huyhoanghust/Final-Project/DATASHEET/RS232_9_pin_D.png

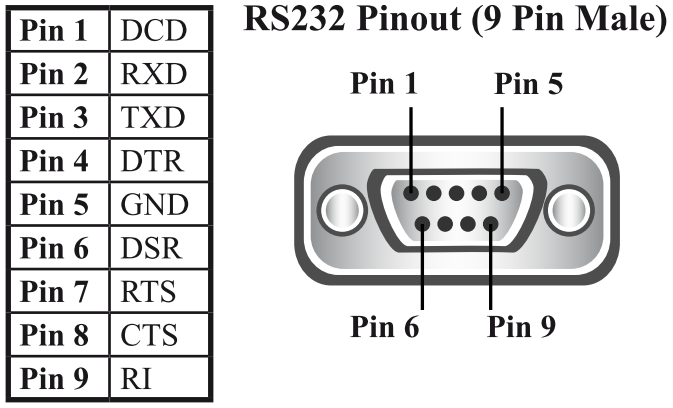
DATASHEET/RS232_9_pin_D.png
