huyhoanghust/Final-Project/DATASHEET/tps54260.png

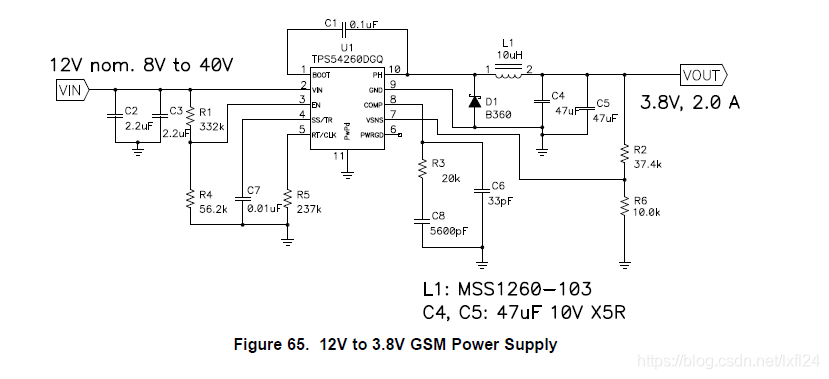
DATASHEET/tps54260.png
