huyhoanghust/Final-Project/DOCUMENT/PICTURE/bang-ky-su-cap-thoat-nuoc-2.jpeg

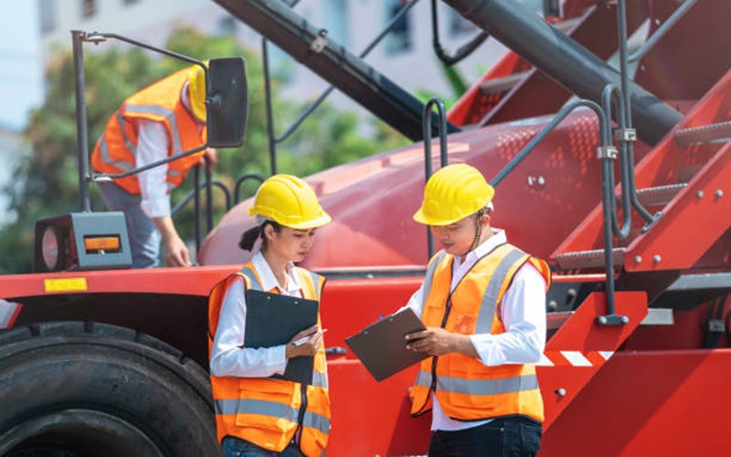
DOCUMENT/PICTURE/bang-ky-su-cap-thoat-nuoc-2.jpeg
