huyhoanghust/Final-Project/DOCUMENT/PICTURE/{1DA086E6-415D-411F-91D1-63A72A324FEF}.png.jpg

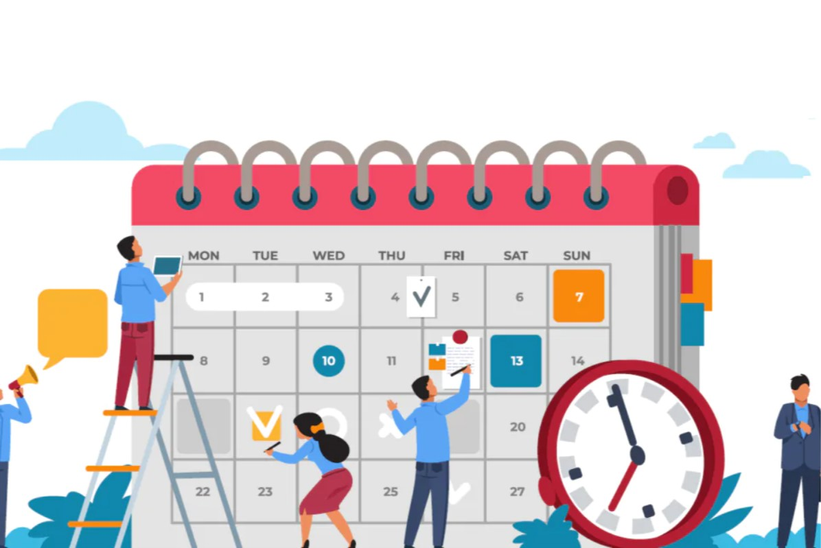
DOCUMENT/PICTURE/{1DA086E6-415D-411F-91D1-63A72A324FEF}.png.jpg
