huyhoanghust/Final-Project/DOCUMENT/PICTURE/{3720CE3A-4CB5-49F4-AB9C-371806BE8C6B}.png.jpg

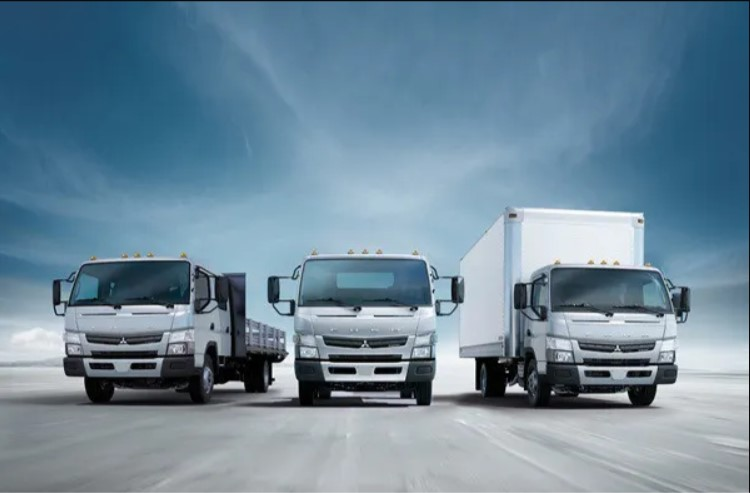
DOCUMENT/PICTURE/{3720CE3A-4CB5-49F4-AB9C-371806BE8C6B}.png.jpg
