huyhoanghust/Final-Project/DOCUMENT/PICTURE/{B581A70F-E1D5-4213-A3DD-116B70B1F578}.png.jpg

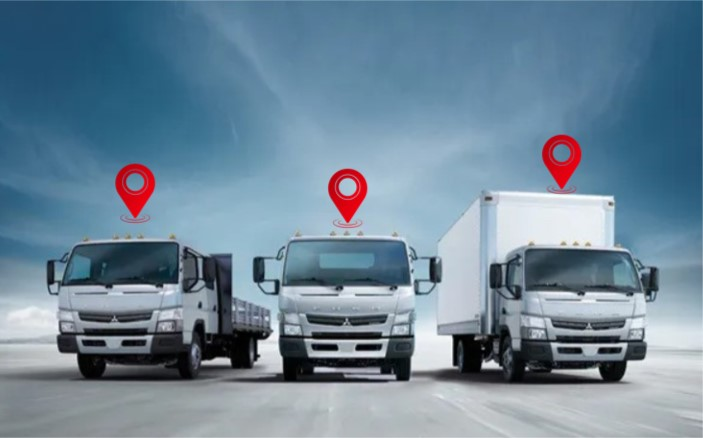
DOCUMENT/PICTURE/{B581A70F-E1D5-4213-A3DD-116B70B1F578}.png.jpg
