huyhoanghust/Final-Project/DOCUMENT/PICTURE/{C75D569E-5FCE-4055-875E-4021B6C22FDB}.png.jpg

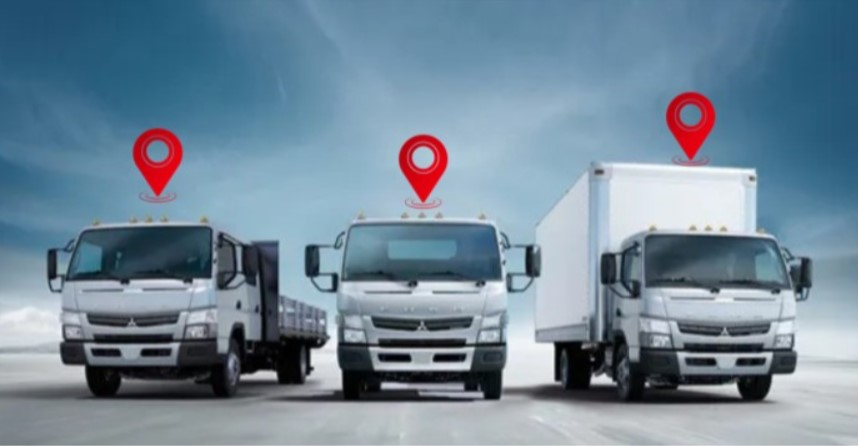
DOCUMENT/PICTURE/{C75D569E-5FCE-4055-875E-4021B6C22FDB}.png.jpg
