huyhoanghust/Final-Project/kế hoạch BVTN.jpg

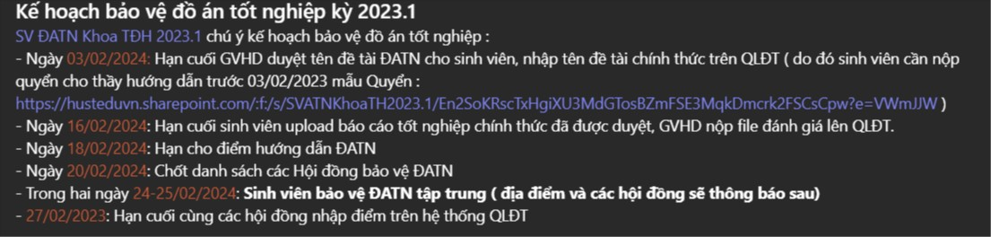
kế hoạch BVTN.jpg
