huyhoanghust/Final-Project/PICTURE/44d2d4de8f7726297f664.jpg

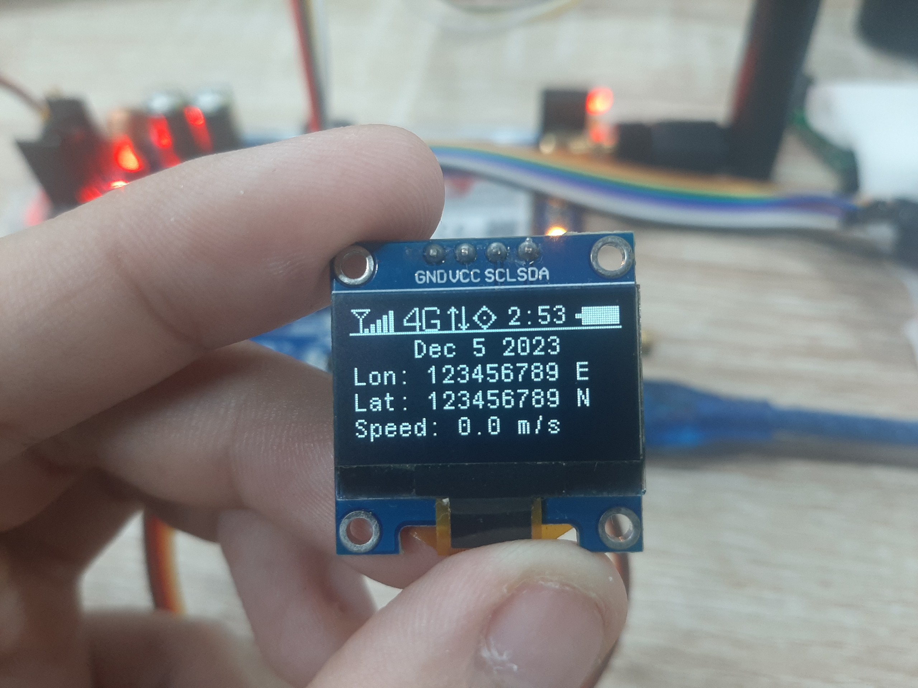
PICTURE/44d2d4de8f7726297f664.jpg
