huyhoanghust/Final-Project/PICTURE/93d33e26648fcdd1949e1.jpg

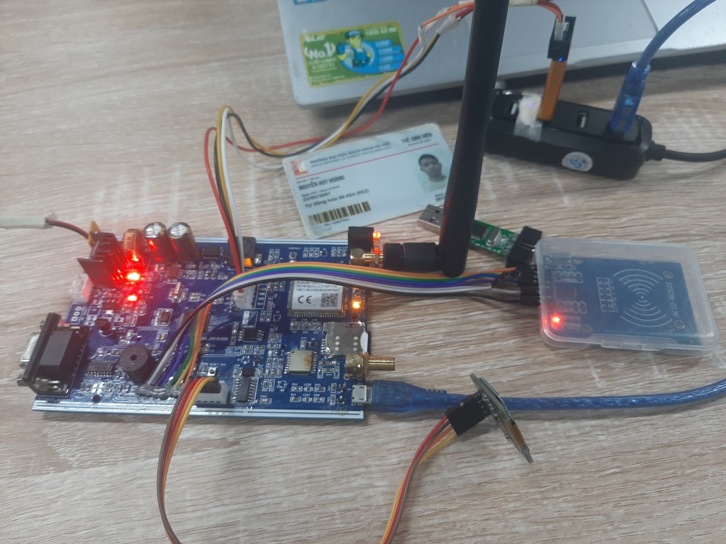
PICTURE/93d33e26648fcdd1949e1.jpg
