huyhoanghust/Final-Project/PICTURE/c10f670b3ca295fcccb33.jpg

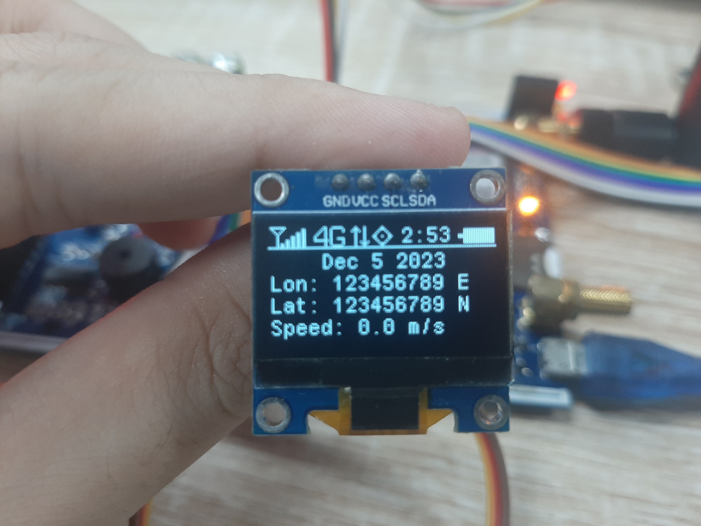
PICTURE/c10f670b3ca295fcccb33.jpg
