huyhoanghust/Final-Project/PICTURE/dfdee423be8a17d44e9b2.jpg

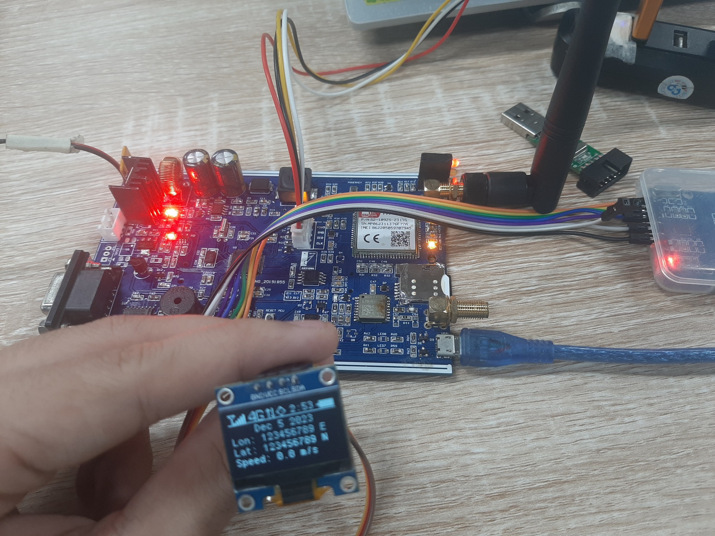
PICTURE/dfdee423be8a17d44e9b2.jpg
