huyhoanghust/Final-Project/PICTURE/f30cfbd6628cc9d2909d.jpg

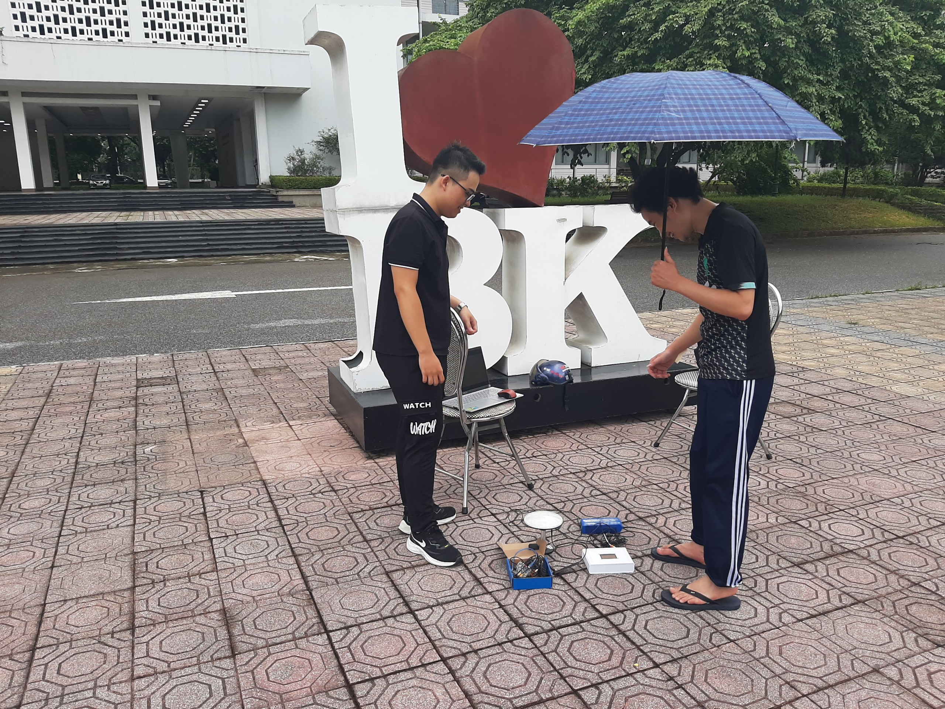
PICTURE/f30cfbd6628cc9d2909d.jpg
