huyhoanghust/Final-Project/PICTURE/firm/ĐATN-firm1.drawio.png

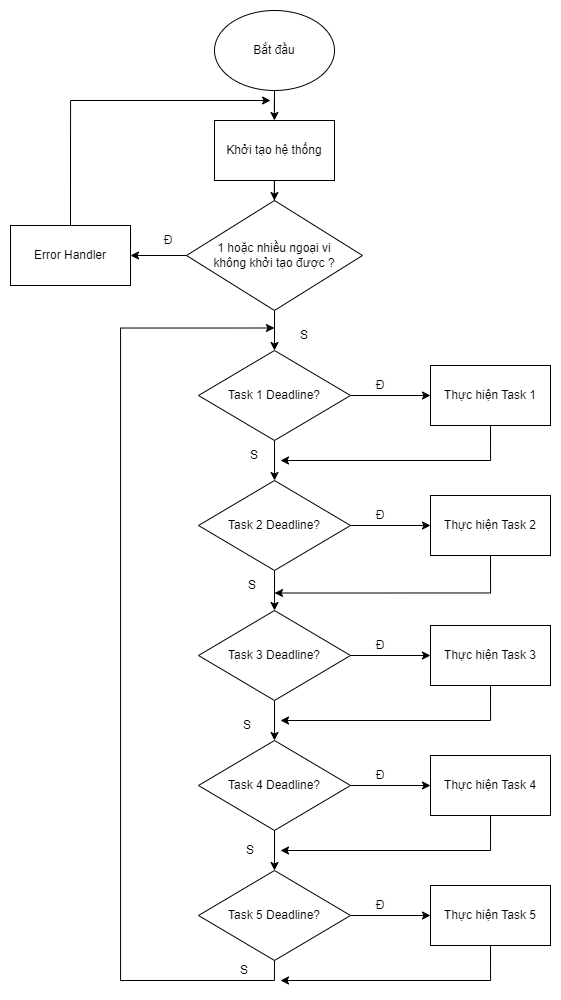
PICTURE/firm/ĐATN-firm1.drawio.png
