huyhoanghust/Final-Project/PICTURE/firm/ĐATN-firm2.drawio.png

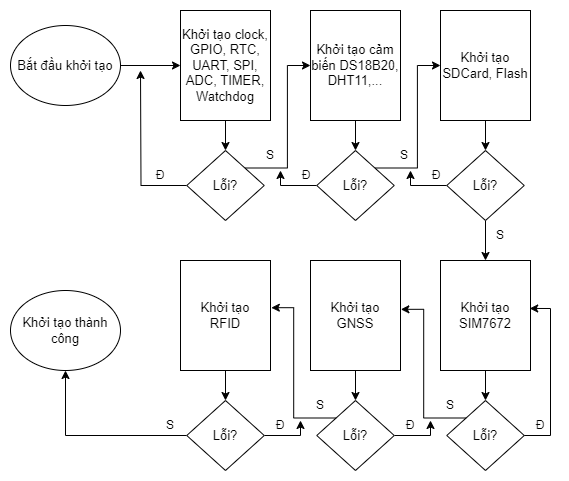
PICTURE/firm/ĐATN-firm2.drawio.png
