huyhoanghust/Final-Project/PICTURE/gnss/bản tin MTK NMEA.jpg

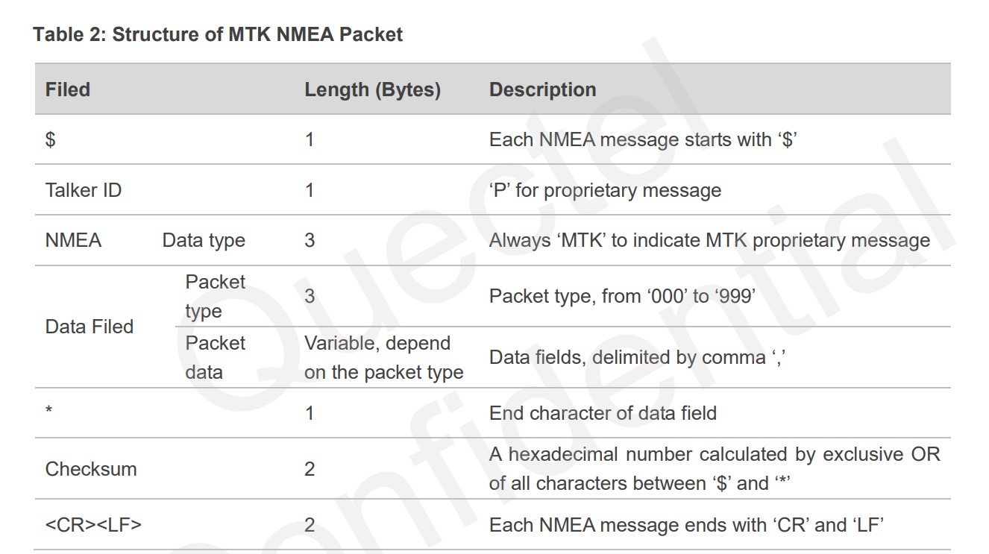
PICTURE/gnss/bản tin MTK NMEA.jpg
