huyhoanghust/Final-Project/PICTURE/gnss/bản tin NMEA.jpg

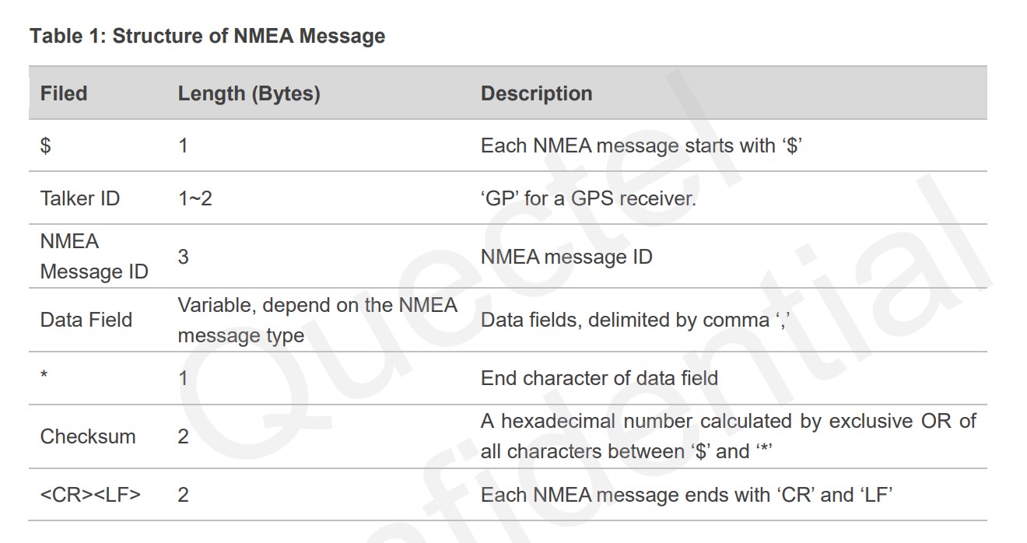
PICTURE/gnss/bản tin NMEA.jpg
