huyhoanghust/Final-Project/PICTURE/gnss/decodeer.jpg

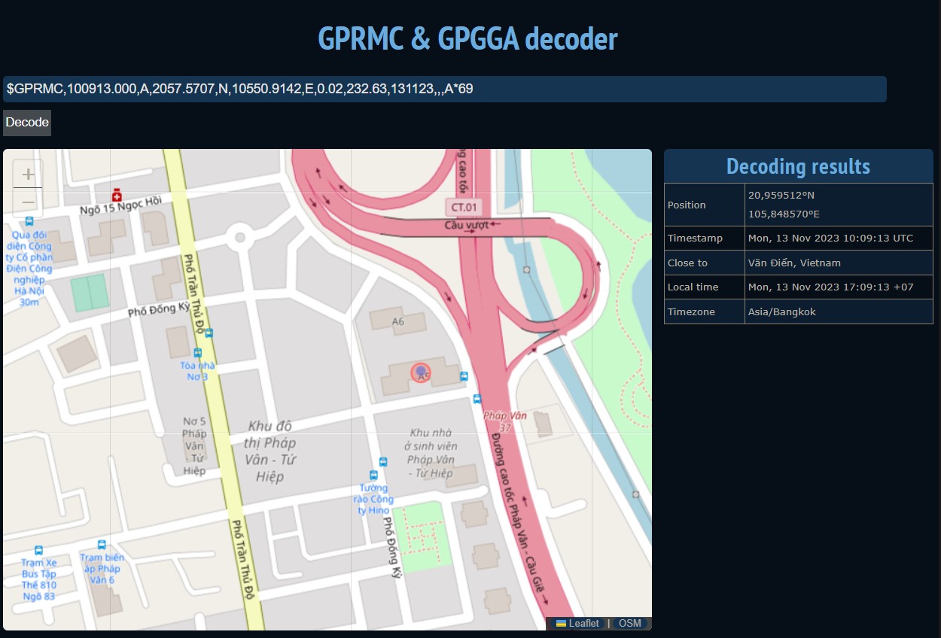
PICTURE/gnss/decodeer.jpg
