huyhoanghust/Final-Project/PICTURE/gnss/{8CABD70A-028F-4958-99A2-55783BED586A}.png.jpg

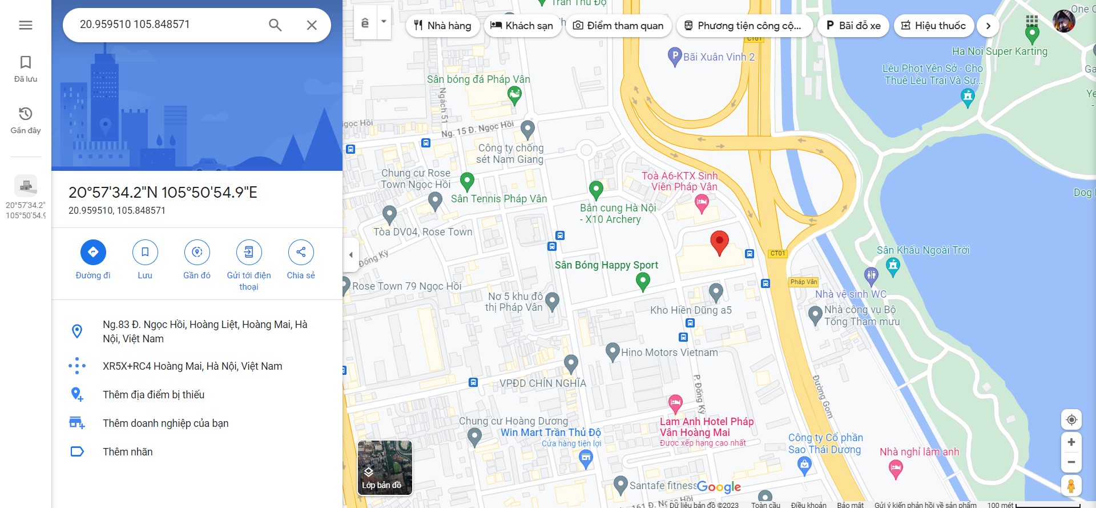
PICTURE/gnss/{8CABD70A-028F-4958-99A2-55783BED586A}.png.jpg
