huyhoanghust/Final-Project/PICTURE/gnss/{868871F9-2B1D-4495-A387-216AAB7A92D2}.png.jpg

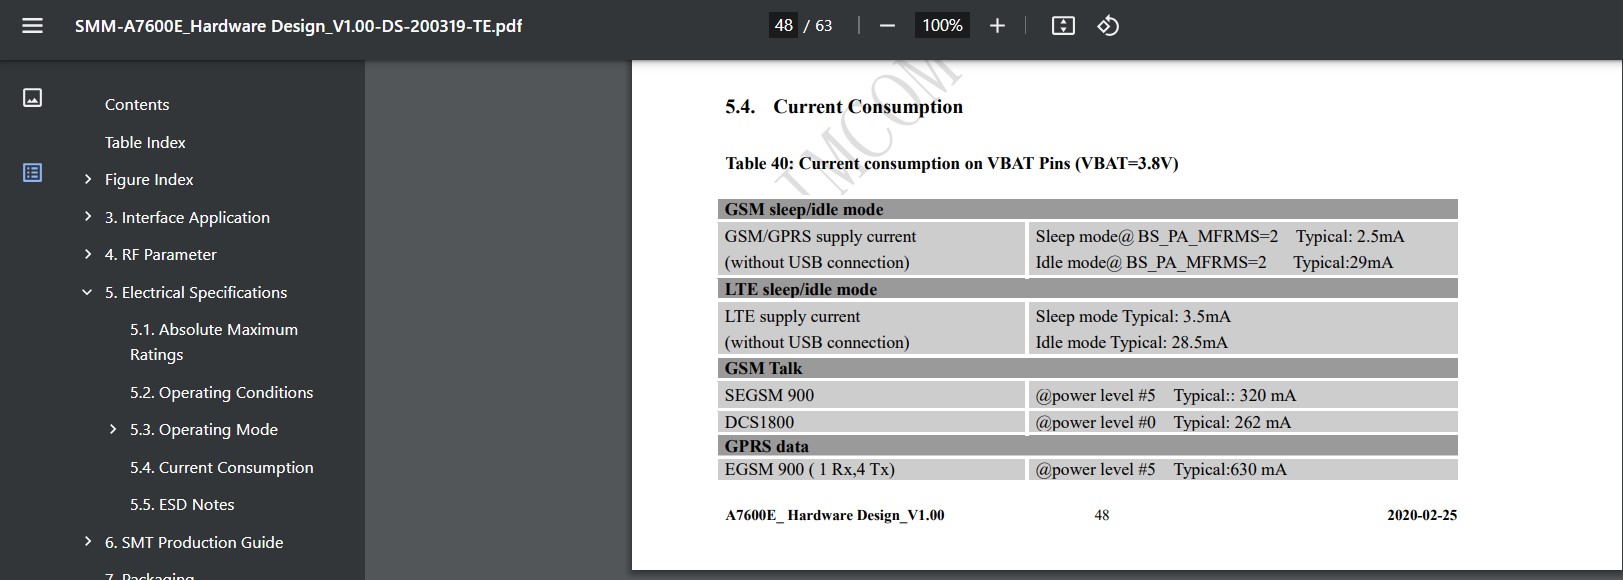
PICTURE/gnss/{868871F9-2B1D-4495-A387-216AAB7A92D2}.png.jpg
