huyhoanghust/Final-Project/PICTURE/gnss/ĐATN-l70_command.drawio.png

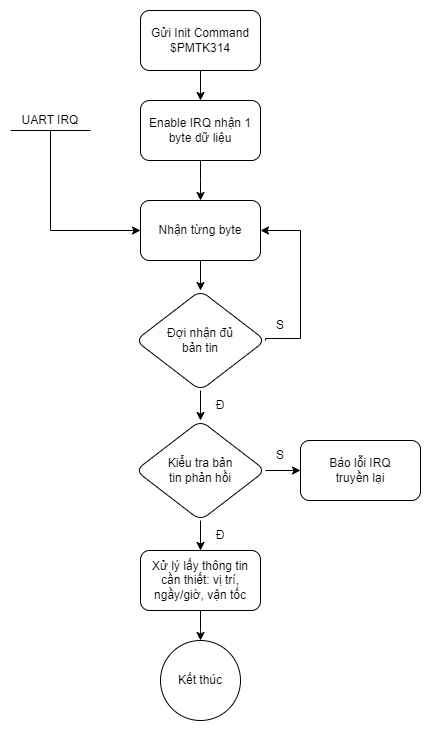
PICTURE/gnss/ĐATN-l70_command.drawio.png
