huyhoanghust/Final-Project/PICTURE/hộp/6137ed7632019a5fc31013.jpg

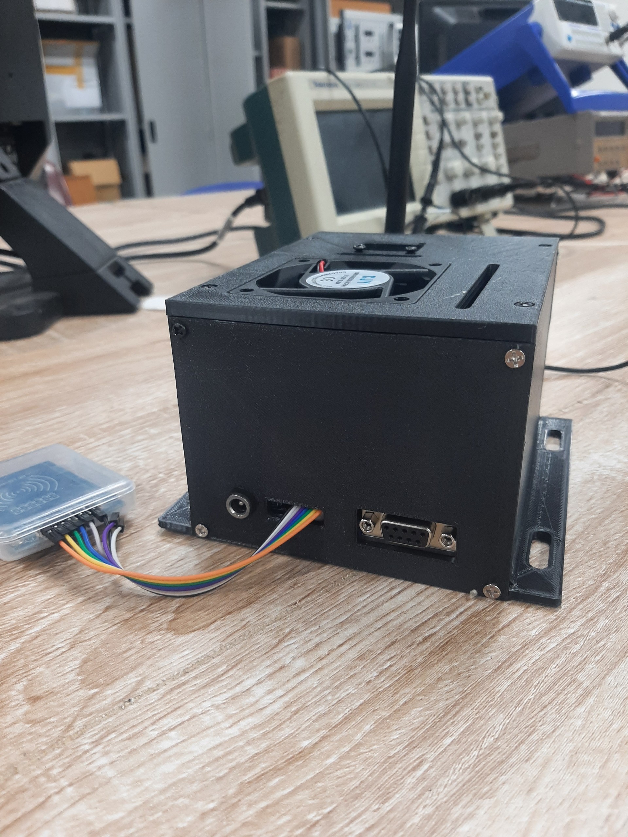
PICTURE/hộp/6137ed7632019a5fc31013.jpg
