huyhoanghust/Final-Project/PICTURE/hộp/64983ceee3994bc7128814.jpg

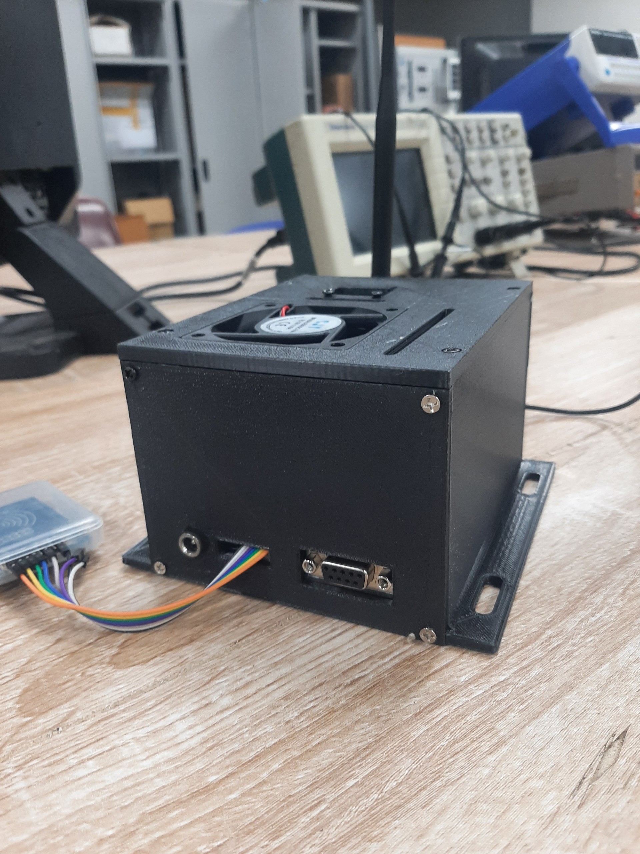
PICTURE/hộp/64983ceee3994bc7128814.jpg
