huyhoanghust/Final-Project/PICTURE/hộp/b8e8435f9c2834766d3911.jpg

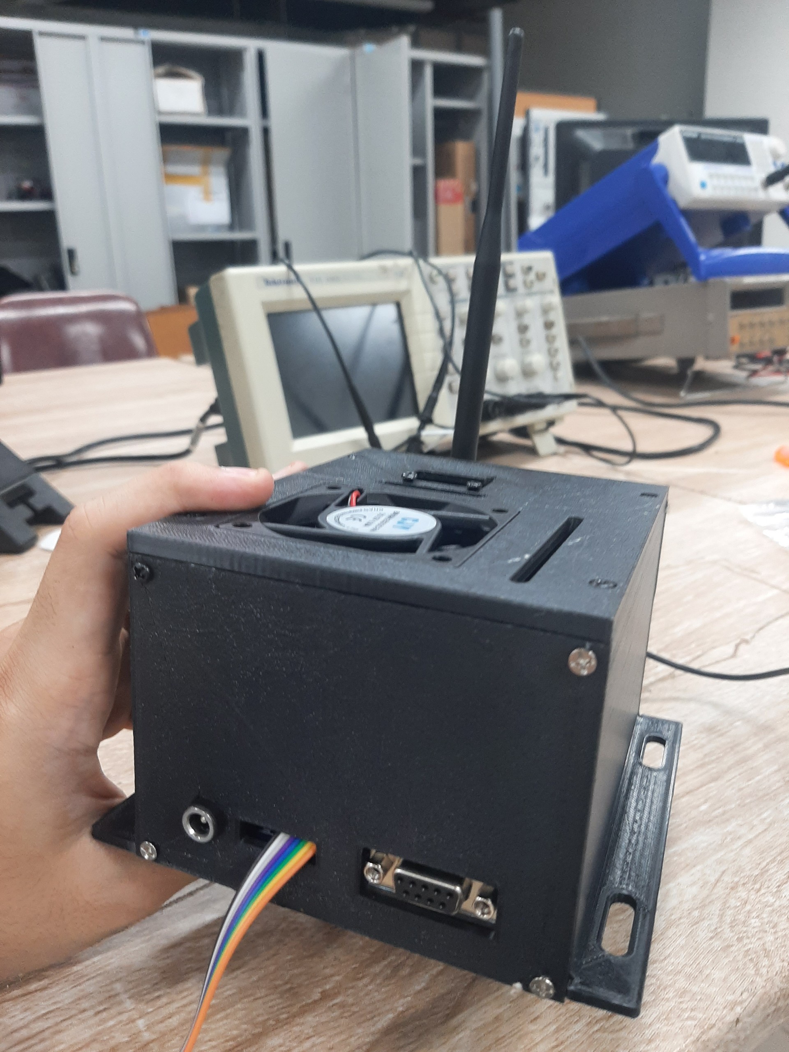
PICTURE/hộp/b8e8435f9c2834766d3911.jpg
