huyhoanghust/Final-Project/PICTURE/hộp/d4fb86a159d6f188a8c712.jpg

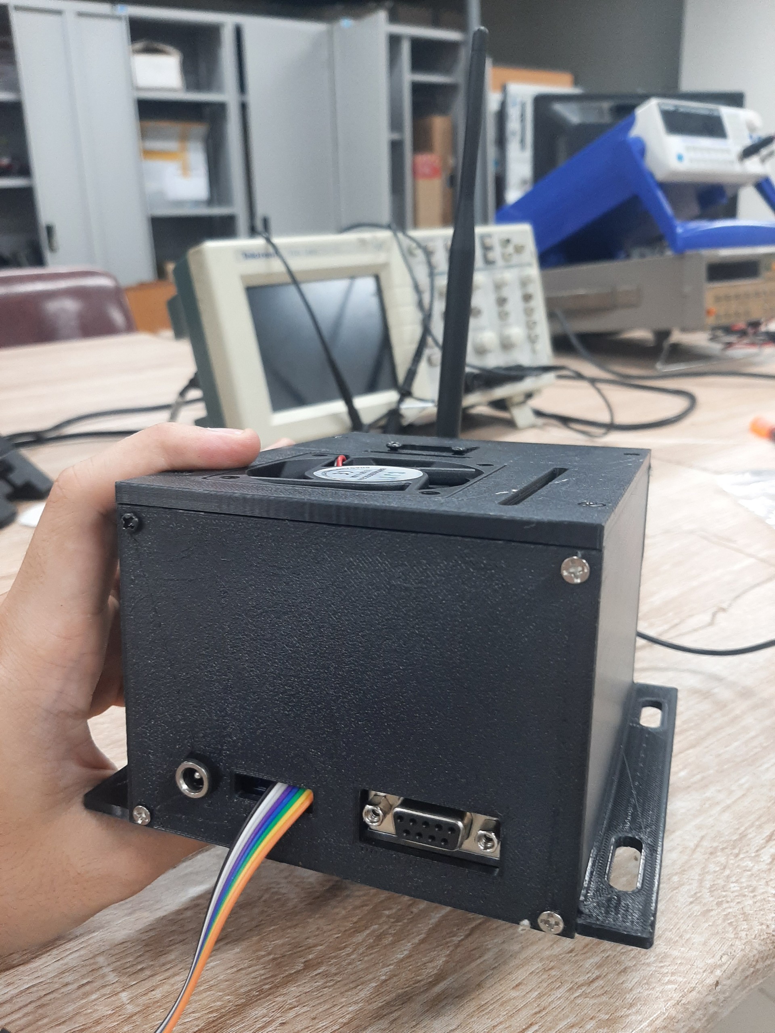
PICTURE/hộp/d4fb86a159d6f188a8c712.jpg
