huyhoanghust/Final-Project/PICTURE/hộp/Vỏ hộp/99a54a46c971602f39606.jpg

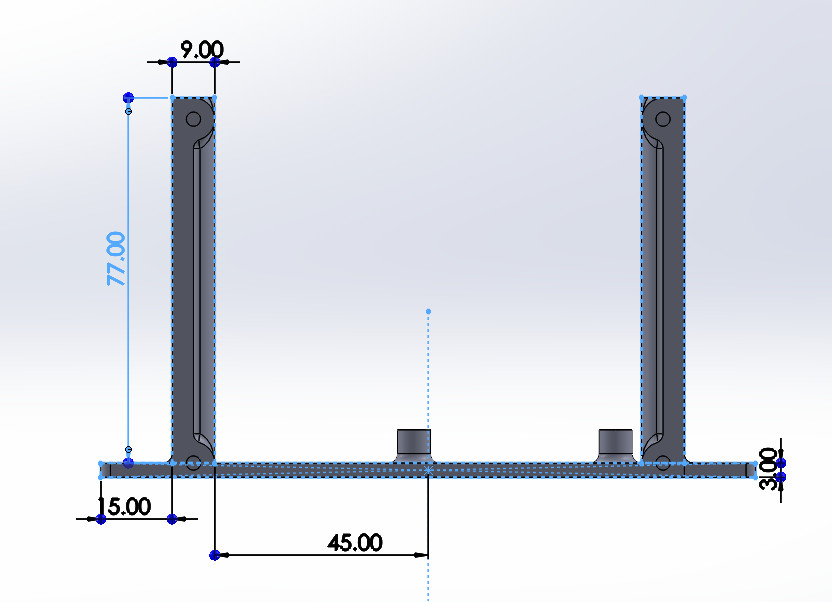
PICTURE/hộp/Vỏ hộp/99a54a46c971602f39606.jpg
