huyhoanghust/Final-Project/PICTURE/hộp/Vỏ hộp/100a95e716d0bf8ee6c15.jpg

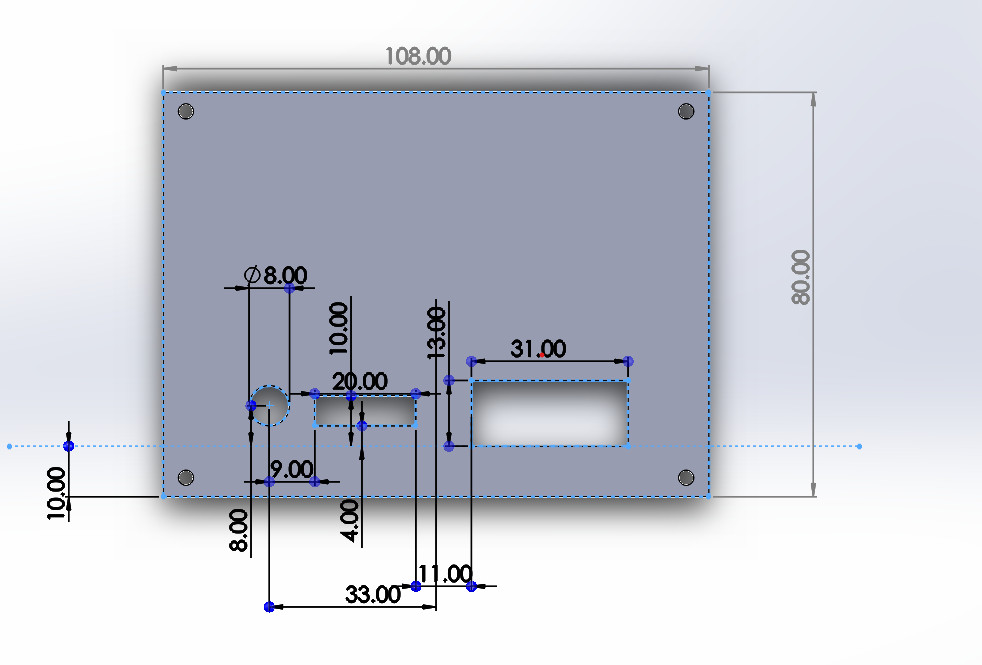
PICTURE/hộp/Vỏ hộp/100a95e716d0bf8ee6c15.jpg
