huyhoanghust/Final-Project/PICTURE/jack.jpeg

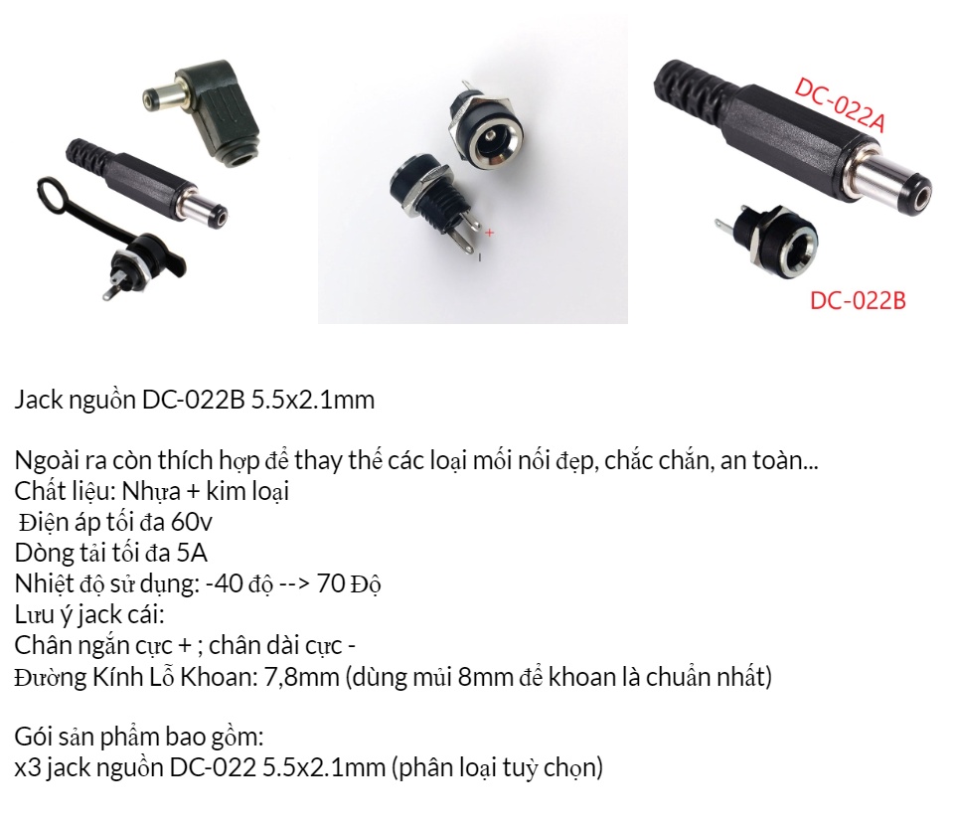
PICTURE/jack.jpeg
