huyhoanghust/Final-Project/PICTURE/kịch bản thử nghiệm/kịch bản 2.jpg

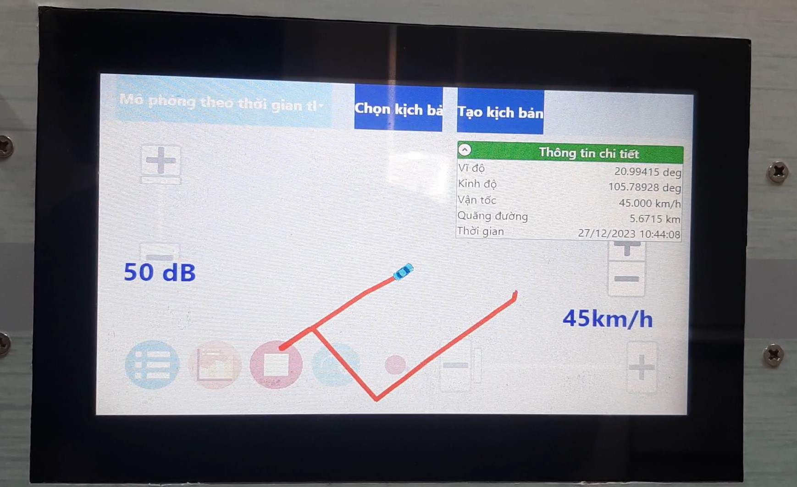
PICTURE/kịch bản thử nghiệm/kịch bản 2.jpg
