huyhoanghust/Final-Project/PICTURE/kịch bản thử nghiệm/máy phát gps.jpg

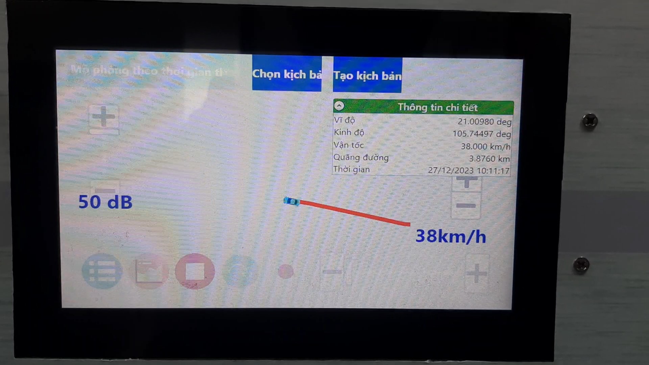
PICTURE/kịch bản thử nghiệm/máy phát gps.jpg
