huyhoanghust/Final-Project/PICTURE/kịch bản thử nghiệm/{20B134B7-DE23-4ED3-82E7-74394B83585F}.png.jpg

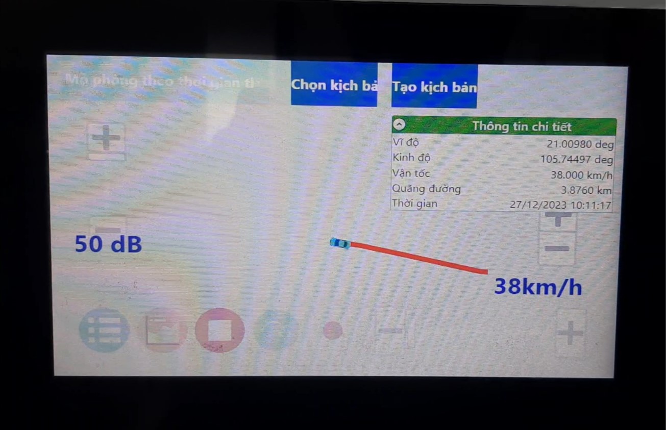
PICTURE/kịch bản thử nghiệm/{20B134B7-DE23-4ED3-82E7-74394B83585F}.png.jpg
