huyhoanghust/Final-Project/PICTURE/kịch bản thử nghiệm/{F6EBA6C6-F068-47A6-98E9-1B882EAFC6DC}.png.jpg

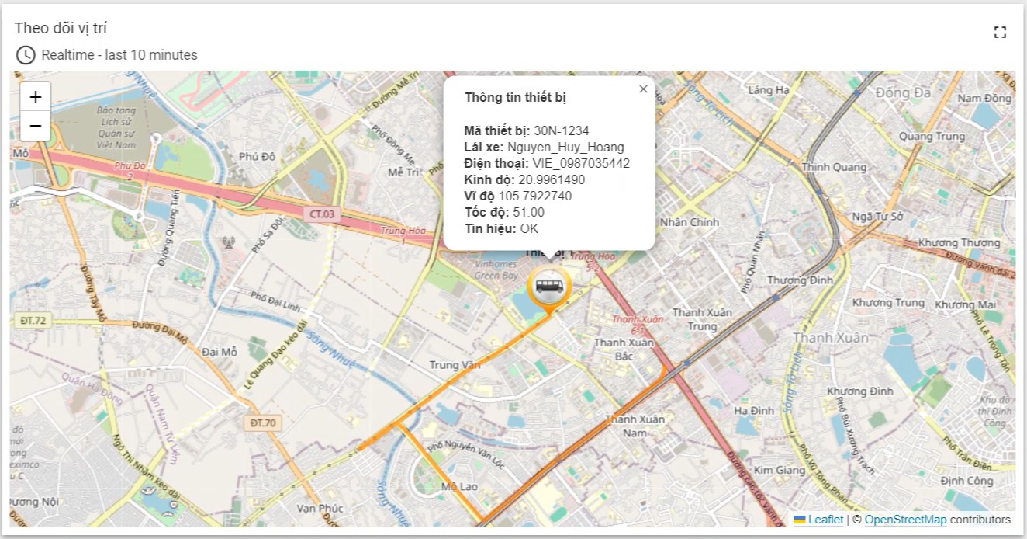
PICTURE/kịch bản thử nghiệm/{F6EBA6C6-F068-47A6-98E9-1B882EAFC6DC}.png.jpg
