huyhoanghust/Final-Project/PICTURE/kịch bản thử nghiệm/đại lộ Thăng Long.jpg

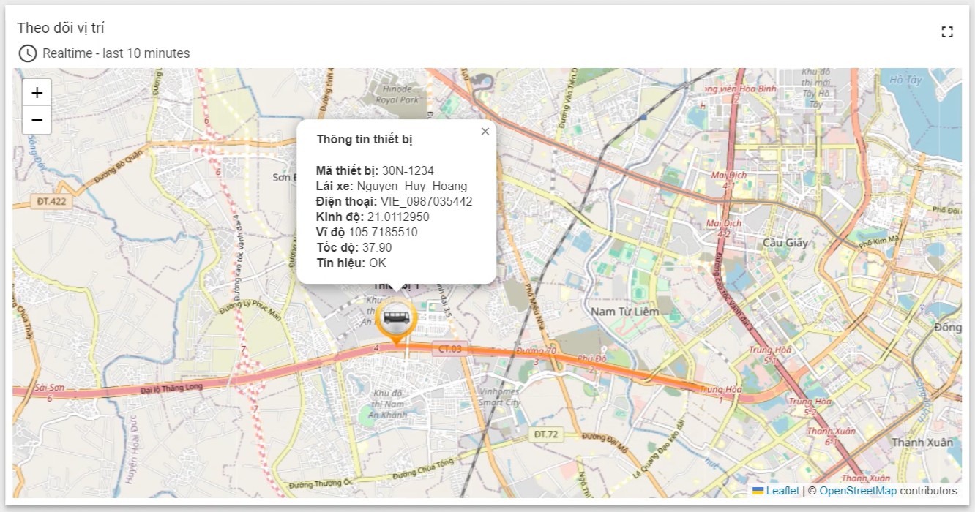
PICTURE/kịch bản thử nghiệm/đại lộ Thăng Long.jpg
