huyhoanghust/Final-Project/PICTURE/Netlight.jpg

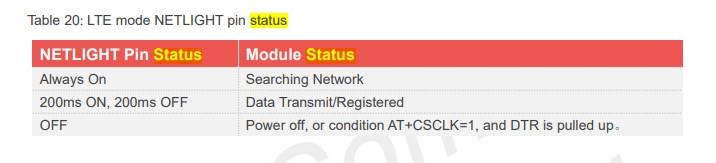
PICTURE/Netlight.jpg
