huyhoanghust/Final-Project/PICTURE/pcb/0be75f5d5223fa7da3328.jpg

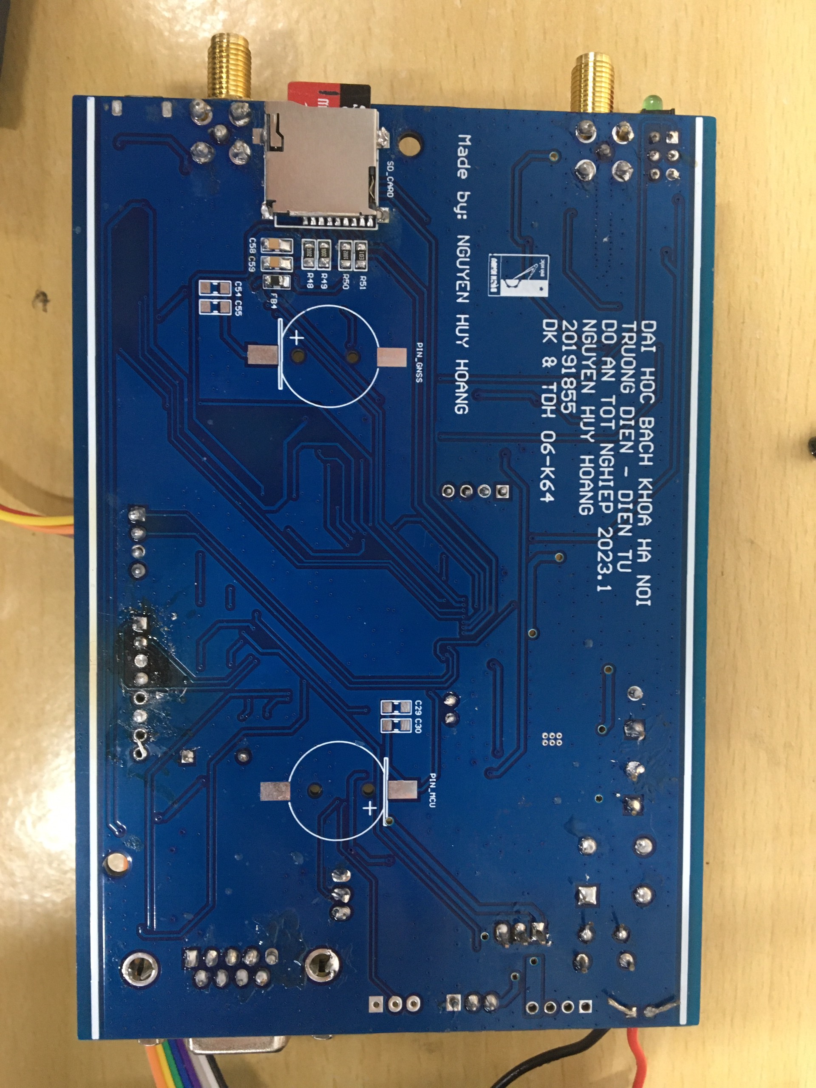
PICTURE/pcb/0be75f5d5223fa7da3328.jpg
