huyhoanghust/Final-Project/PICTURE/pcb/5a7ebb8eb6f01eae47e16.jpg

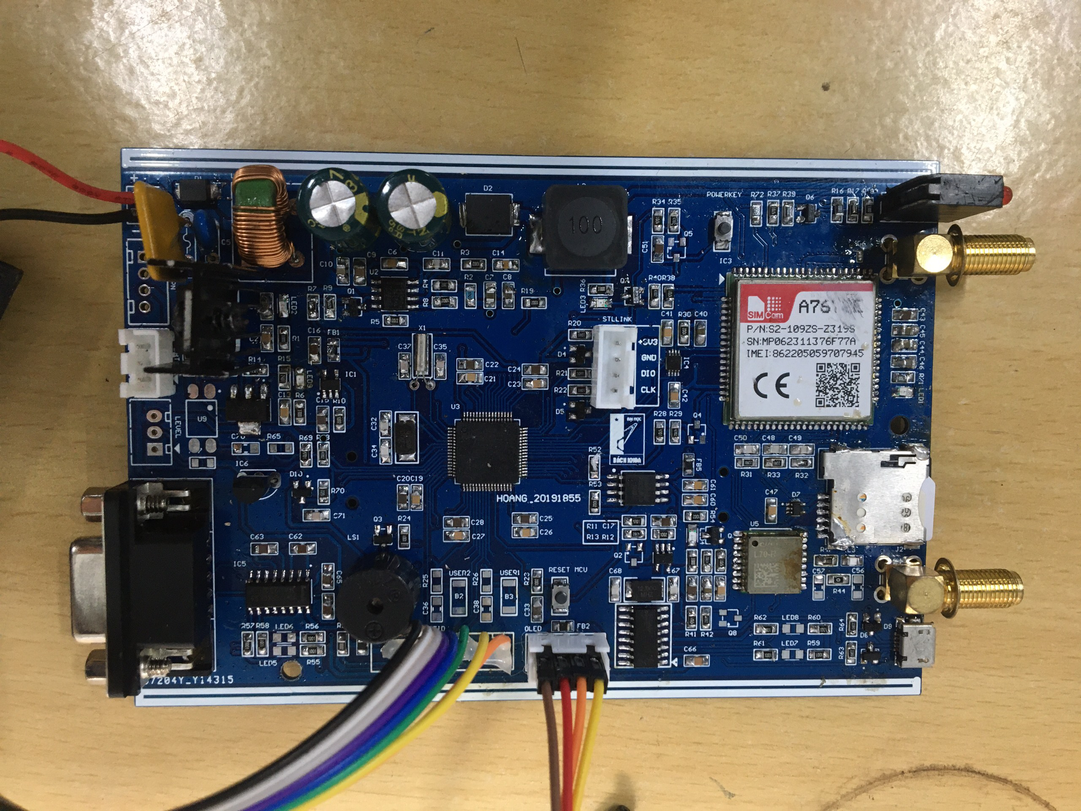
PICTURE/pcb/5a7ebb8eb6f01eae47e16.jpg
