huyhoanghust/Final-Project/PICTURE/pcb/50cbce6cc3126b4c320312.jpg

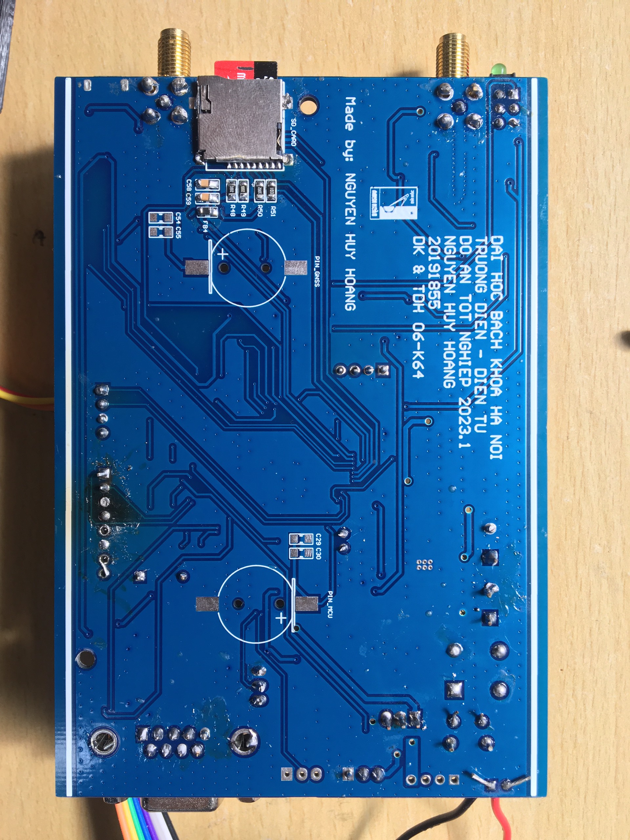
PICTURE/pcb/50cbce6cc3126b4c320312.jpg
