huyhoanghust/Final-Project/PICTURE/pcb/8662be04db1a0d44540b2.jpg

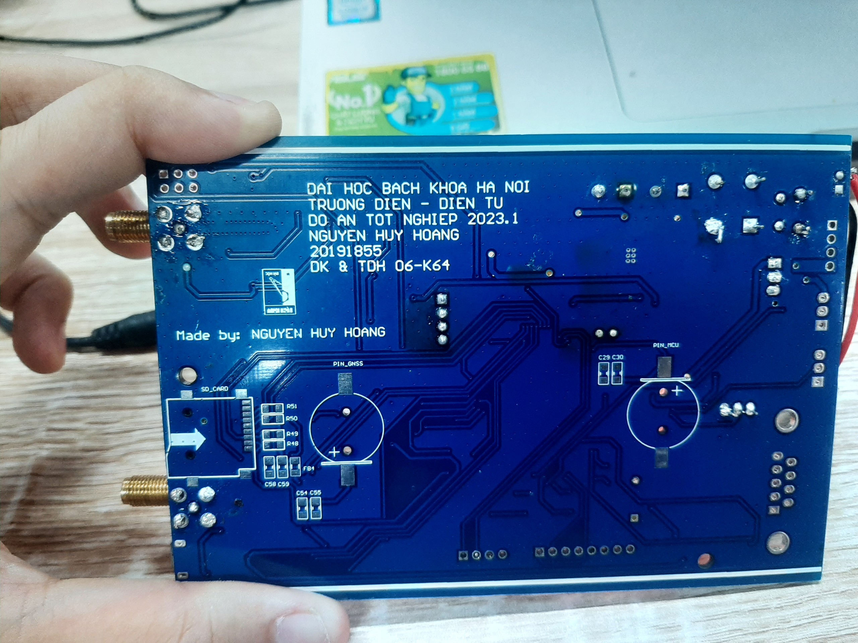
PICTURE/pcb/8662be04db1a0d44540b2.jpg
