huyhoanghust/Final-Project/PICTURE/pcb/9516daacd7d27f8c26c310.jpg

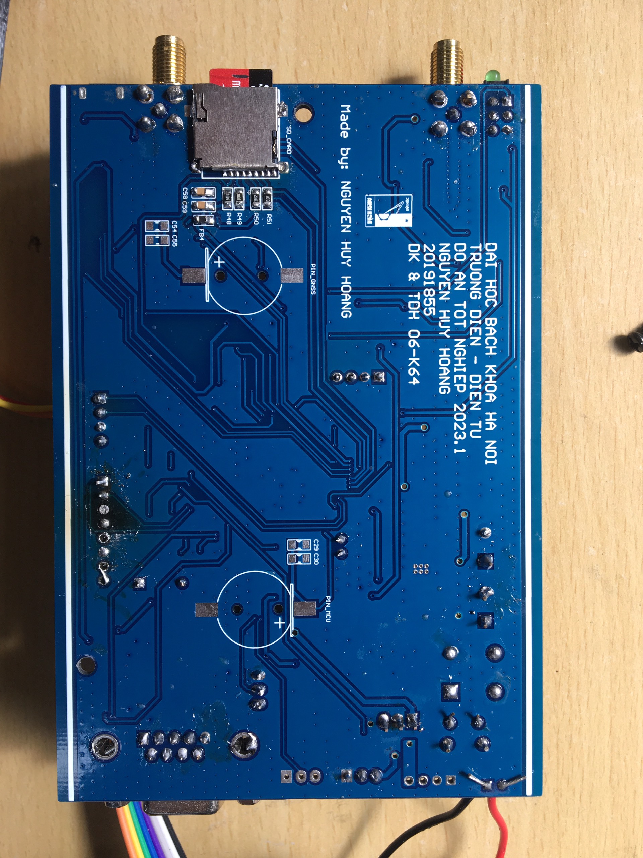
PICTURE/pcb/9516daacd7d27f8c26c310.jpg
