huyhoanghust/Final-Project/PICTURE/pcb/ANT_4G.jpg

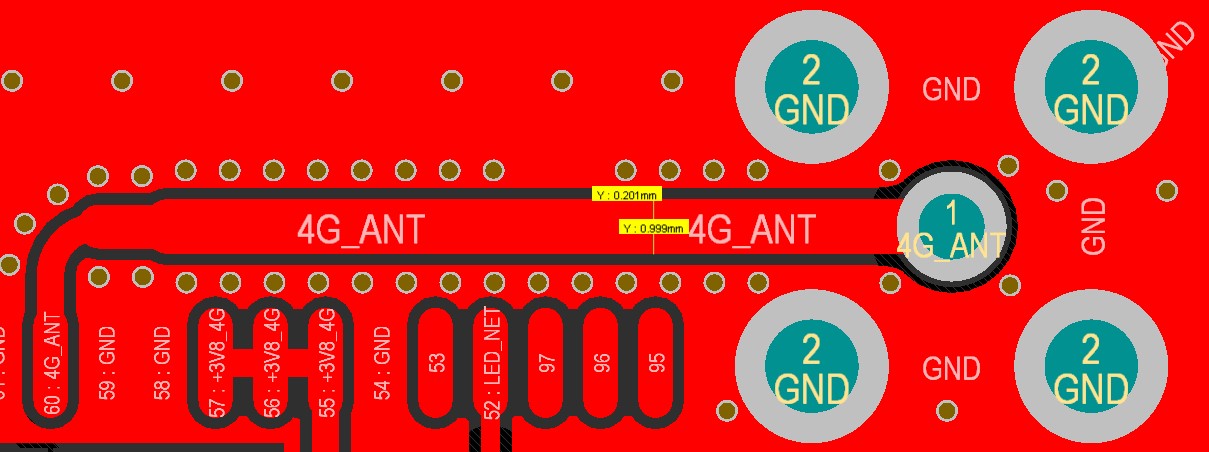
PICTURE/pcb/ANT_4G.jpg
