huyhoanghust/Final-Project/PICTURE/pcb/ANT_GNSS.jpg

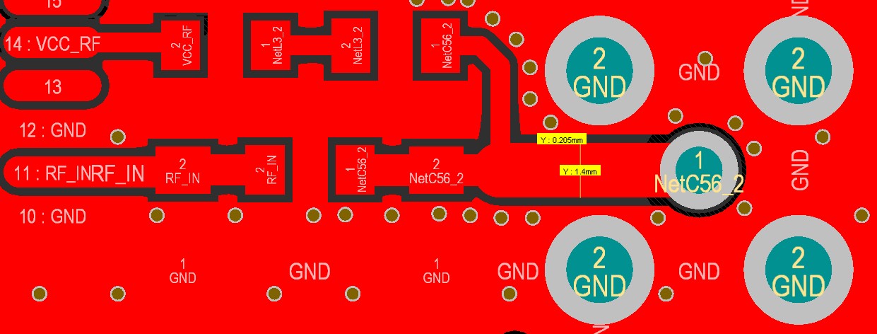
PICTURE/pcb/ANT_GNSS.jpg
