huyhoanghust/Final-Project/PICTURE/pcb/c6c450ba35a4e3fabab51.jpg

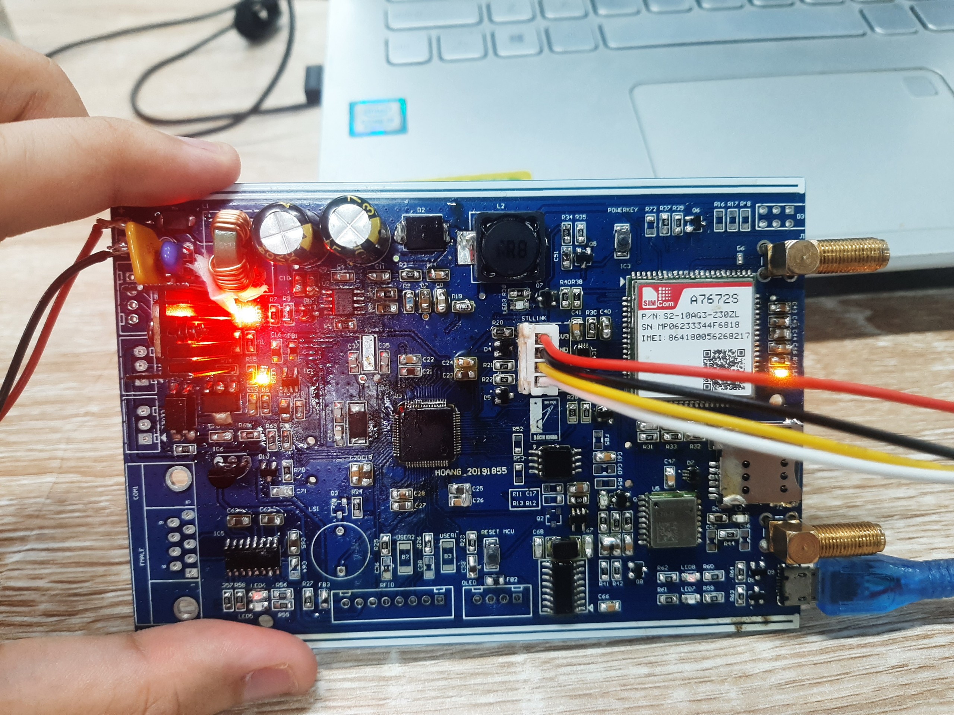
PICTURE/pcb/c6c450ba35a4e3fabab51.jpg
