huyhoanghust/Final-Project/PICTURE/pcb/c69a0ab118cfb091e9de2.jpg

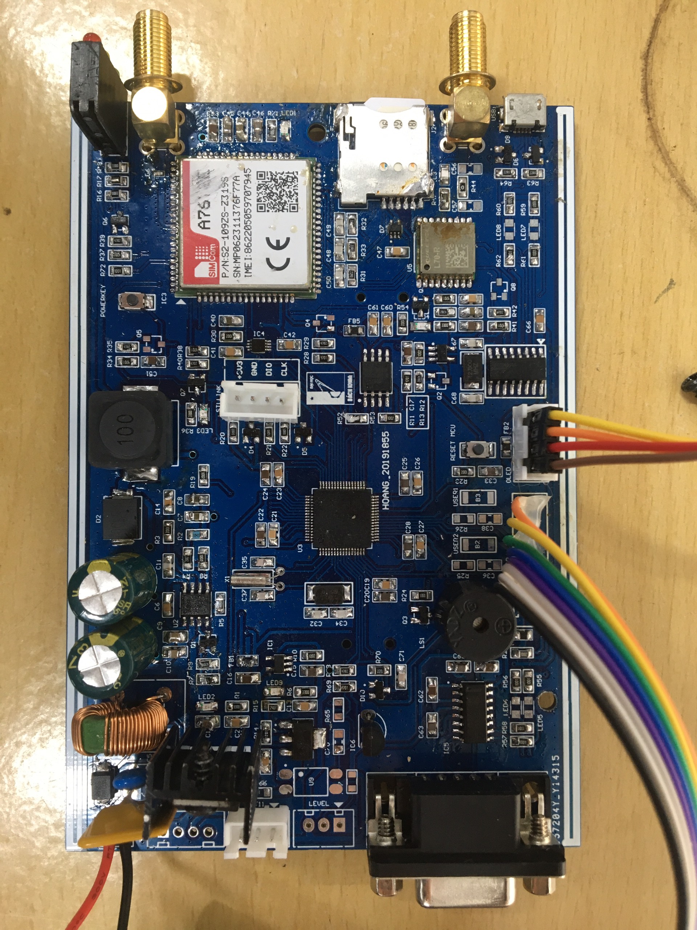
PICTURE/pcb/c69a0ab118cfb091e9de2.jpg
