huyhoanghust/Final-Project/PICTURE/pcb/Cloud của tôi [16-12-2023 14_59]/mặt sau.jpg

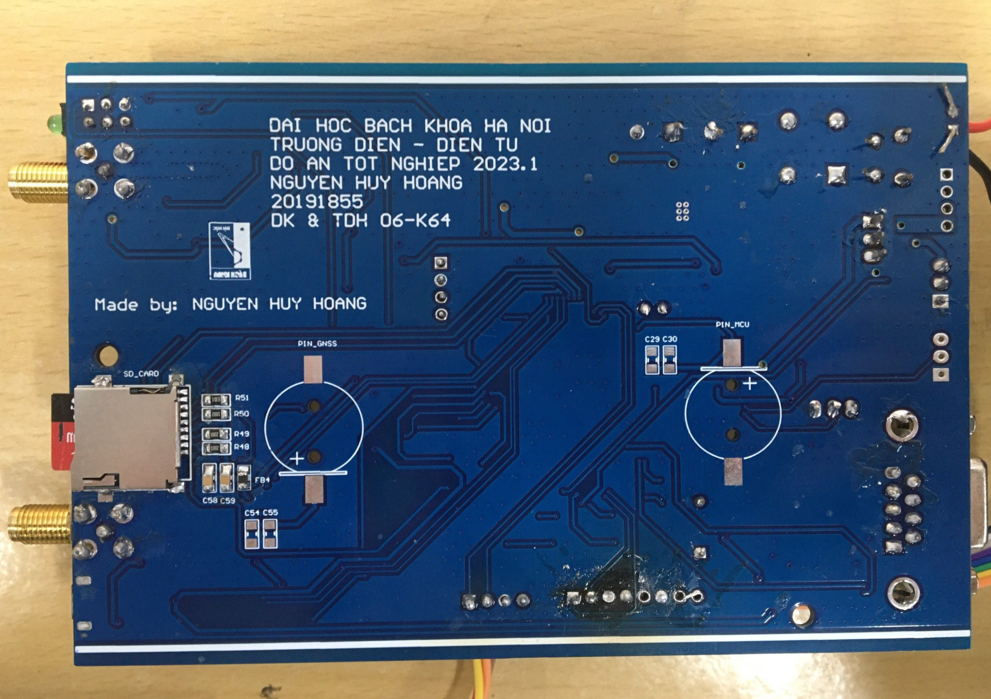
PICTURE/pcb/Cloud của tôi [16-12-2023 14_59]/mặt sau.jpg
