huyhoanghust/Final-Project/PICTURE/pcb/gnss.jpg

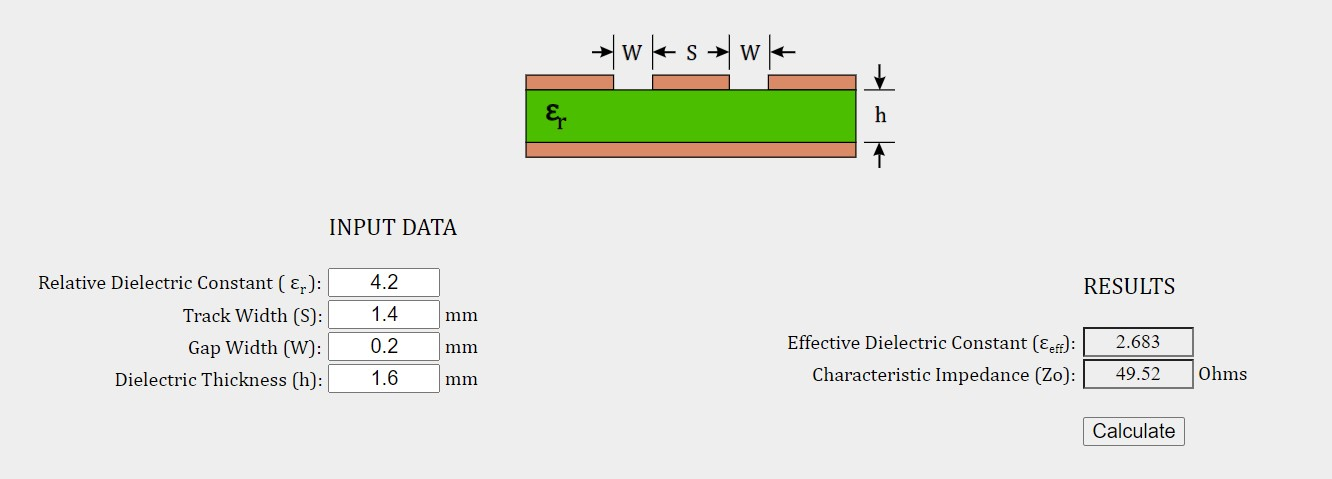
PICTURE/pcb/gnss.jpg
