huyhoanghust/Final-Project/PICTURE/pcb/mặt trước.jpg

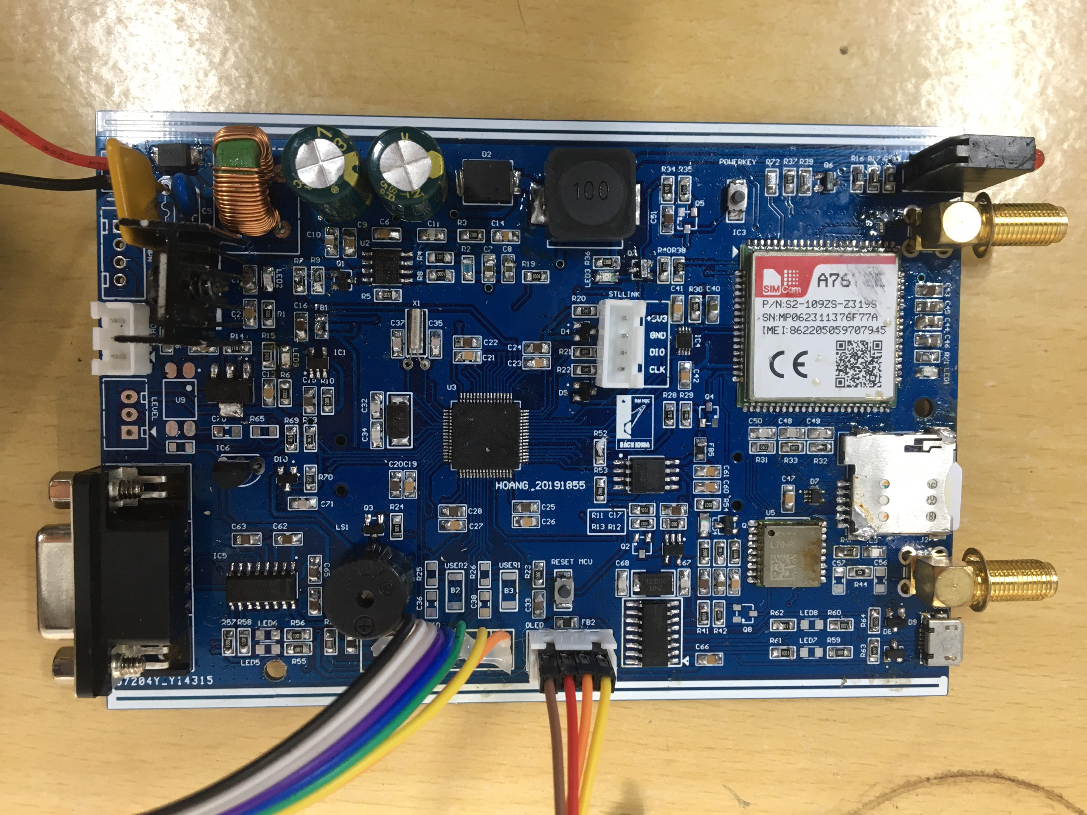
PICTURE/pcb/mặt trước.jpg
