huyhoanghust/Final-Project/PICTURE/pcb/nguồn.jpg

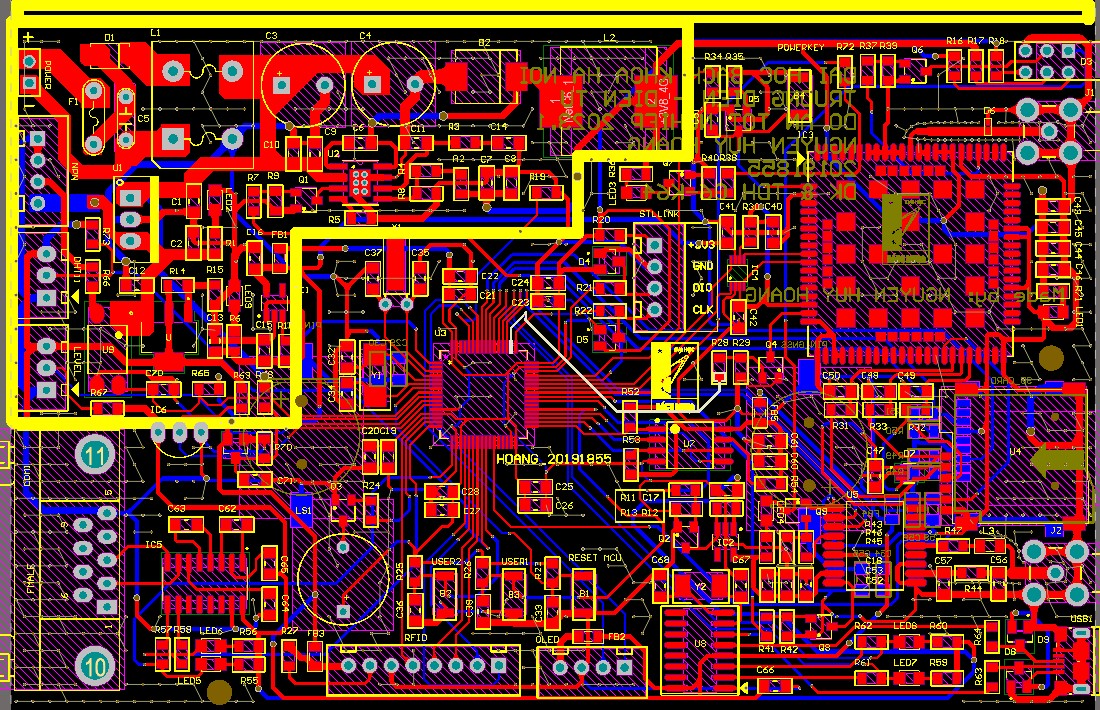
PICTURE/pcb/nguồn.jpg
