huyhoanghust/Final-Project/PICTURE/pcb/pcb1.jpg

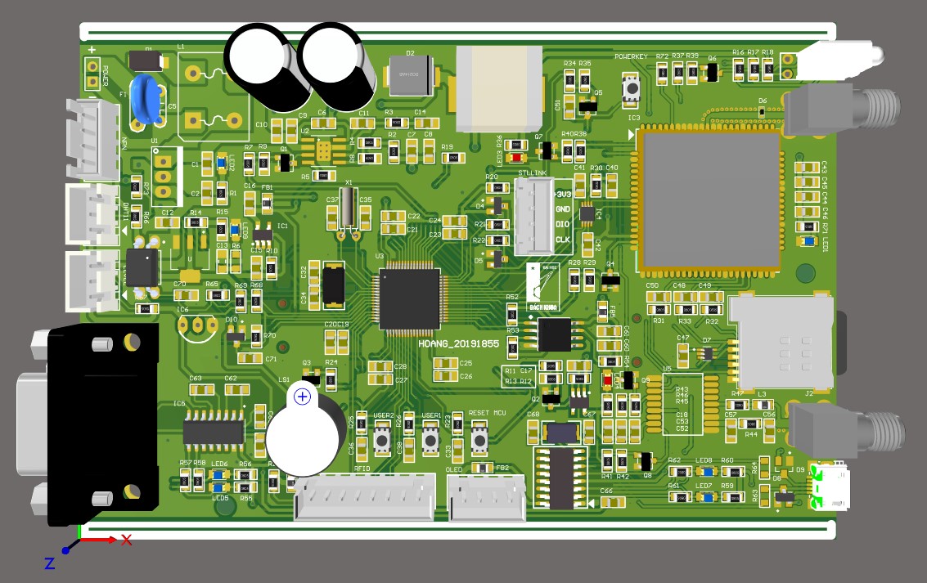
PICTURE/pcb/pcb1.jpg
