huyhoanghust/Final-Project/PICTURE/pcb/pcb2.jpg

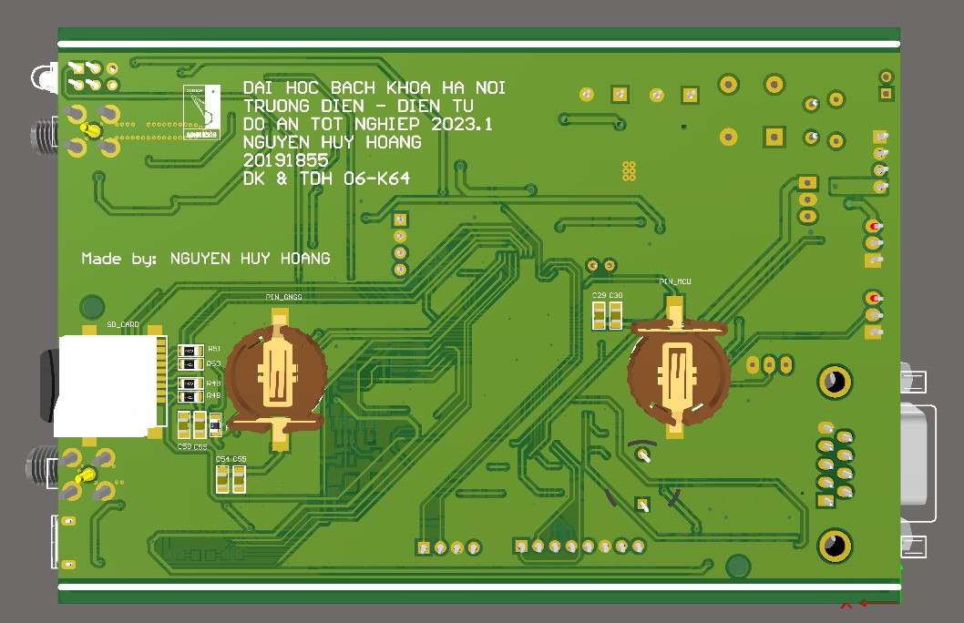
PICTURE/pcb/pcb2.jpg
