huyhoanghust/Final-Project/PICTURE/pcb/pcb3.jpg

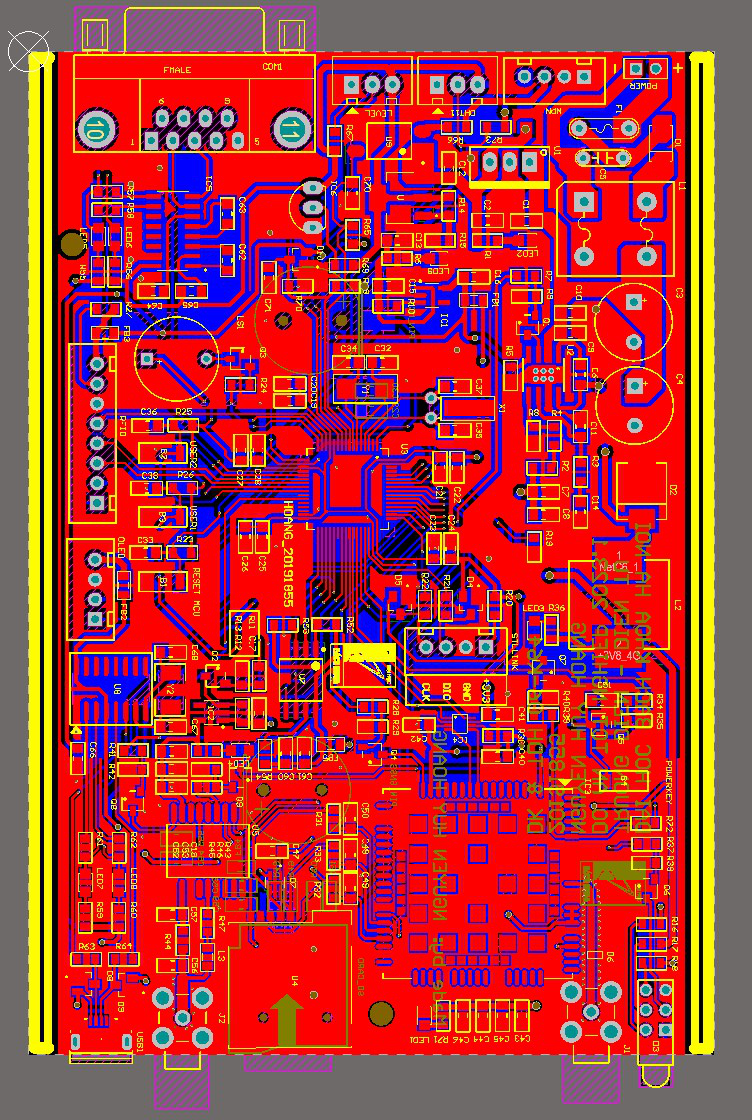
PICTURE/pcb/pcb3.jpg
