huyhoanghust/Final-Project/PICTURE/pcb/pcb4.jpg

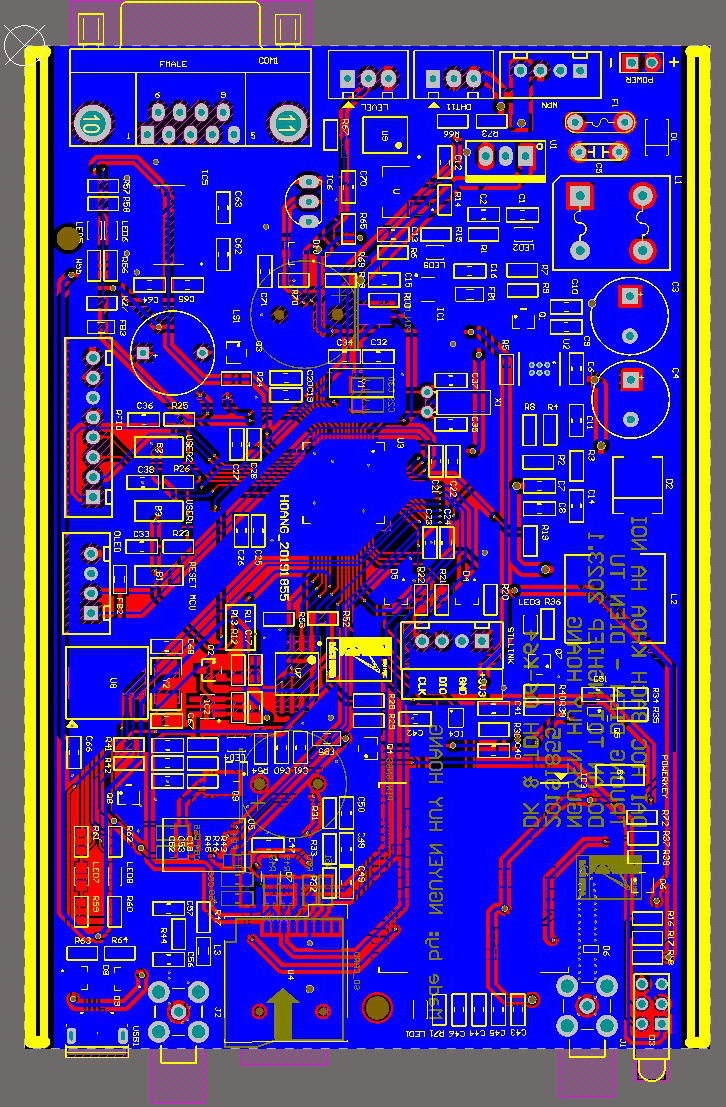
PICTURE/pcb/pcb4.jpg
