huyhoanghust/Final-Project/PICTURE/pcb/pcb.jpg

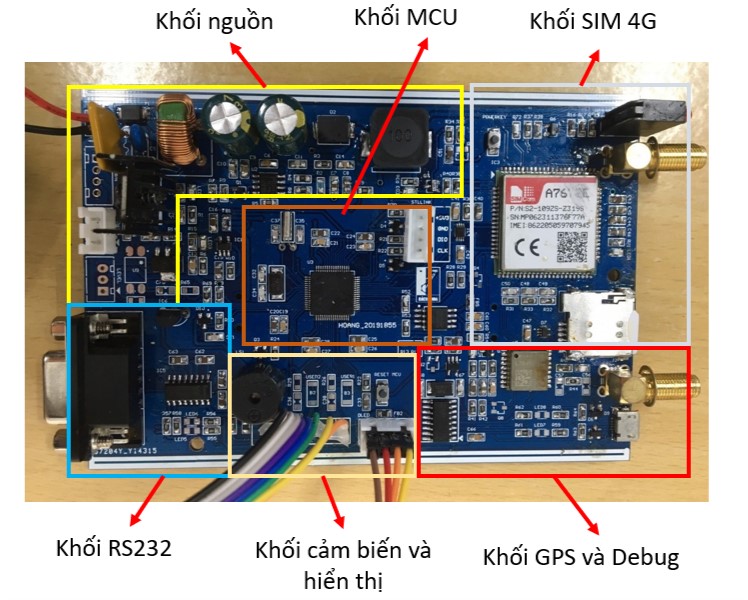
PICTURE/pcb/pcb.jpg
