huyhoanghust/Final-Project/PICTURE/pcb/{CCB55274-613D-4977-BEBF-E9A701A18242}.png.jpg

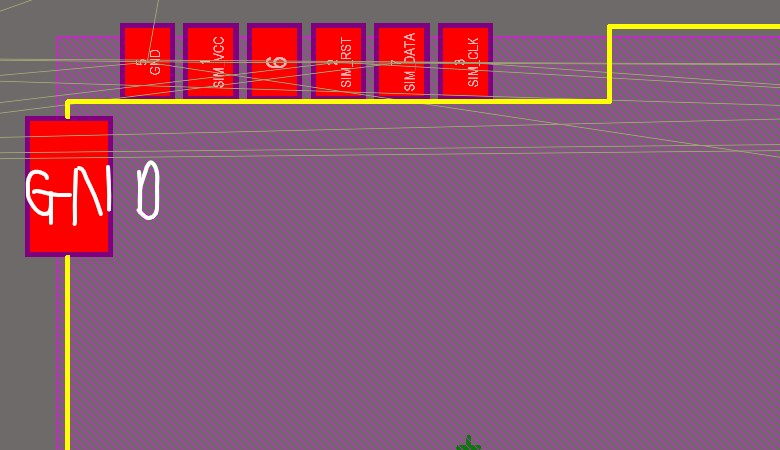
PICTURE/pcb/{CCB55274-613D-4977-BEBF-E9A701A18242}.png.jpg
