huyhoanghust/Final-Project/PICTURE/pcb/ĐATN-2D.drawio.png

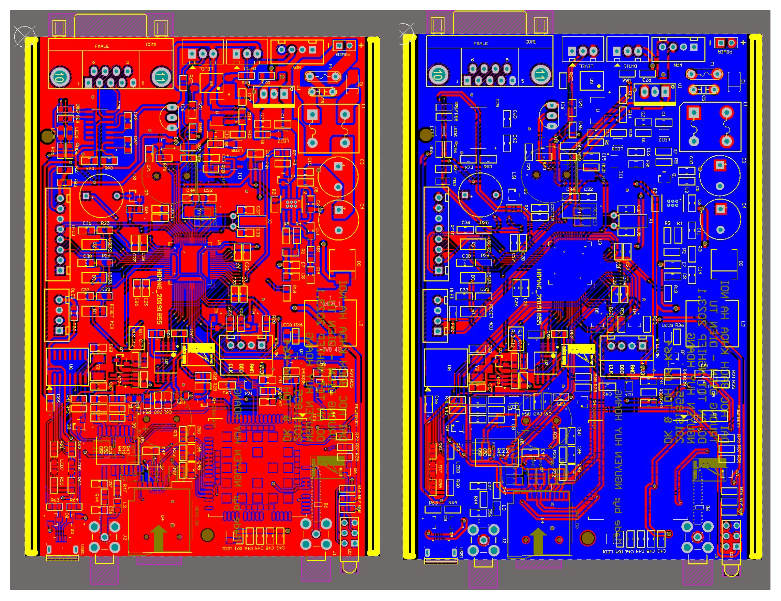
PICTURE/pcb/ĐATN-2D.drawio.png
