huyhoanghust/Final-Project/PICTURE/pcb/ĐATN-3D.drawio.png

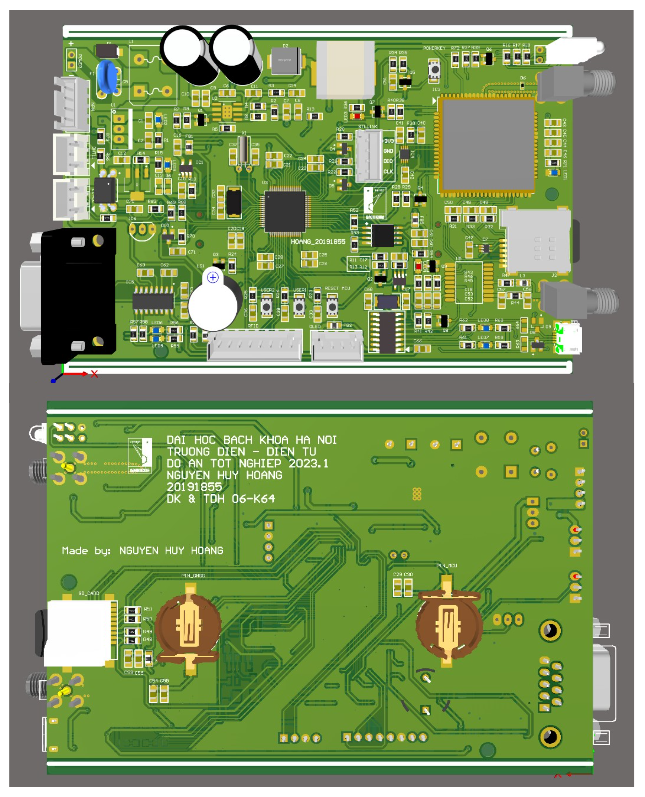
PICTURE/pcb/ĐATN-3D.drawio.png
