huyhoanghust/Final-Project/PICTURE/pcb/ĐATN-Page-5.drawio.png

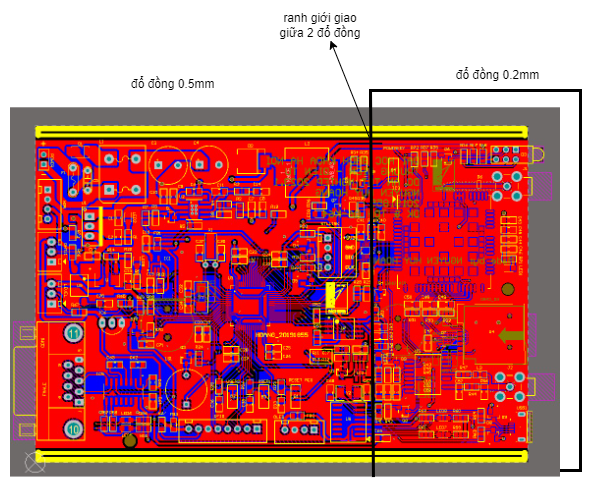
PICTURE/pcb/ĐATN-Page-5.drawio.png
