huyhoanghust/Final-Project/PICTURE/pcb/ĐATN-sơ đồ các khối .drawio.png

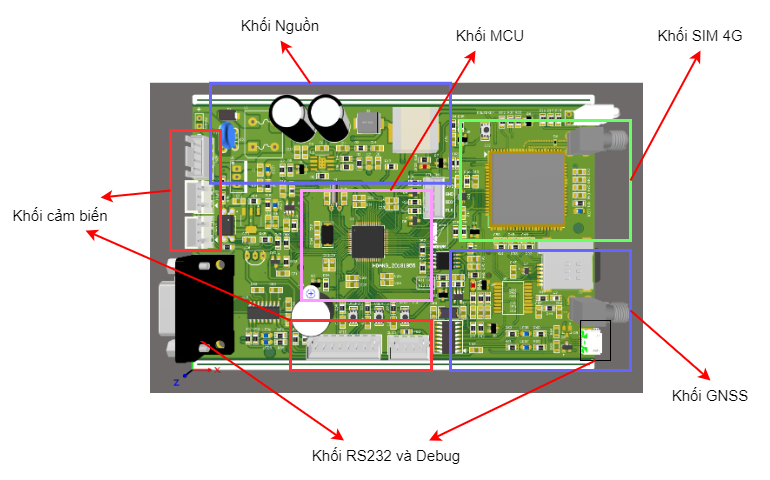
PICTURE/pcb/ĐATN-sơ đồ các khối .drawio.png
