huyhoanghust/Final-Project/PICTURE/pcb/ĐATN-thạch anh.drawio.png

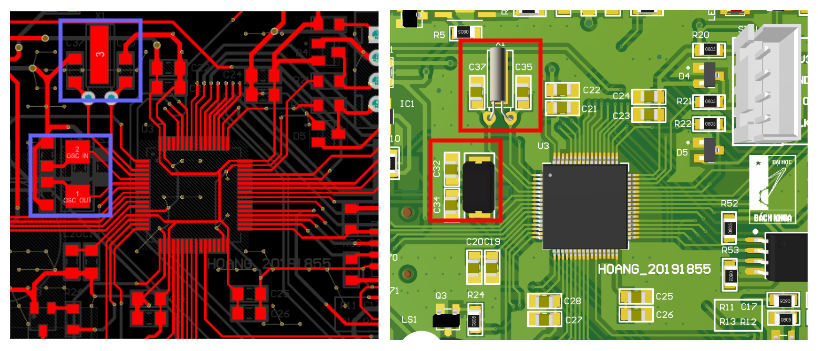
PICTURE/pcb/ĐATN-thạch anh.drawio.png
