huyhoanghust/Final-Project/PICTURE/pcb/ĐATN-tụ.drawio.png

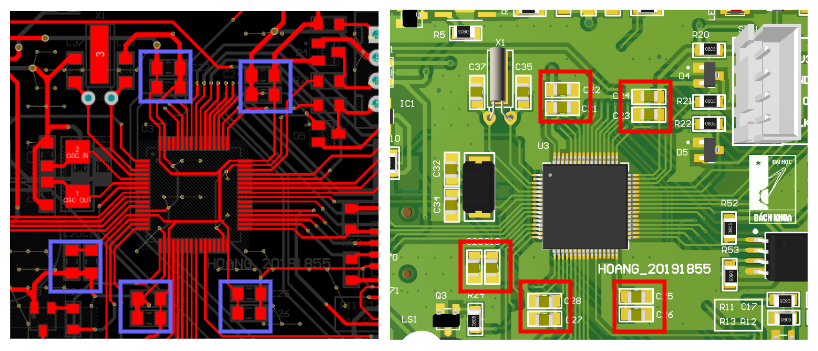
PICTURE/pcb/ĐATN-tụ.drawio.png
