huyhoanghust/Final-Project/PICTURE/ref/4.jpg

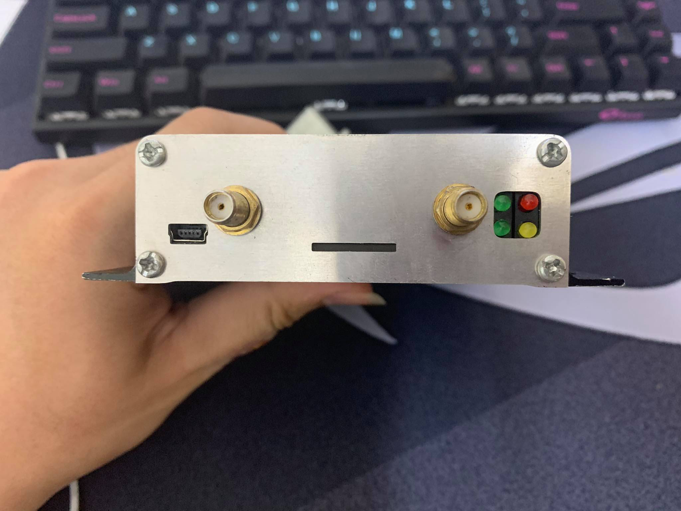
PICTURE/ref/4.jpg
