huyhoanghust/Final-Project/PICTURE/ref/203932265_332078971963298_9100070212533783609_n.jpg

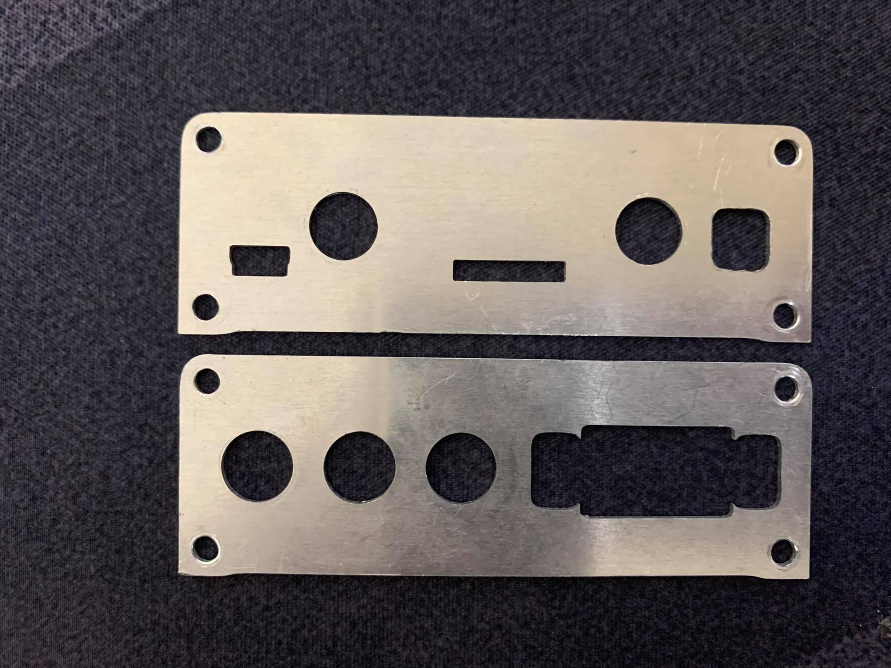
PICTURE/ref/203932265_332078971963298_9100070212533783609_n.jpg
