huyhoanghust/Final-Project/PICTURE/rtk.jpg

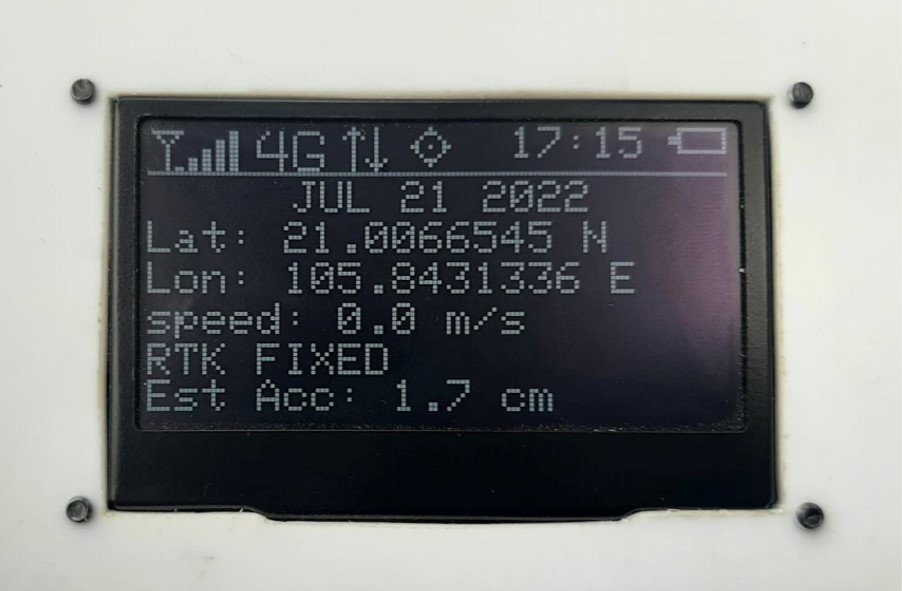
PICTURE/rtk.jpg
