huyhoanghust/Final-Project/PICTURE/sdcard_file2.jpg

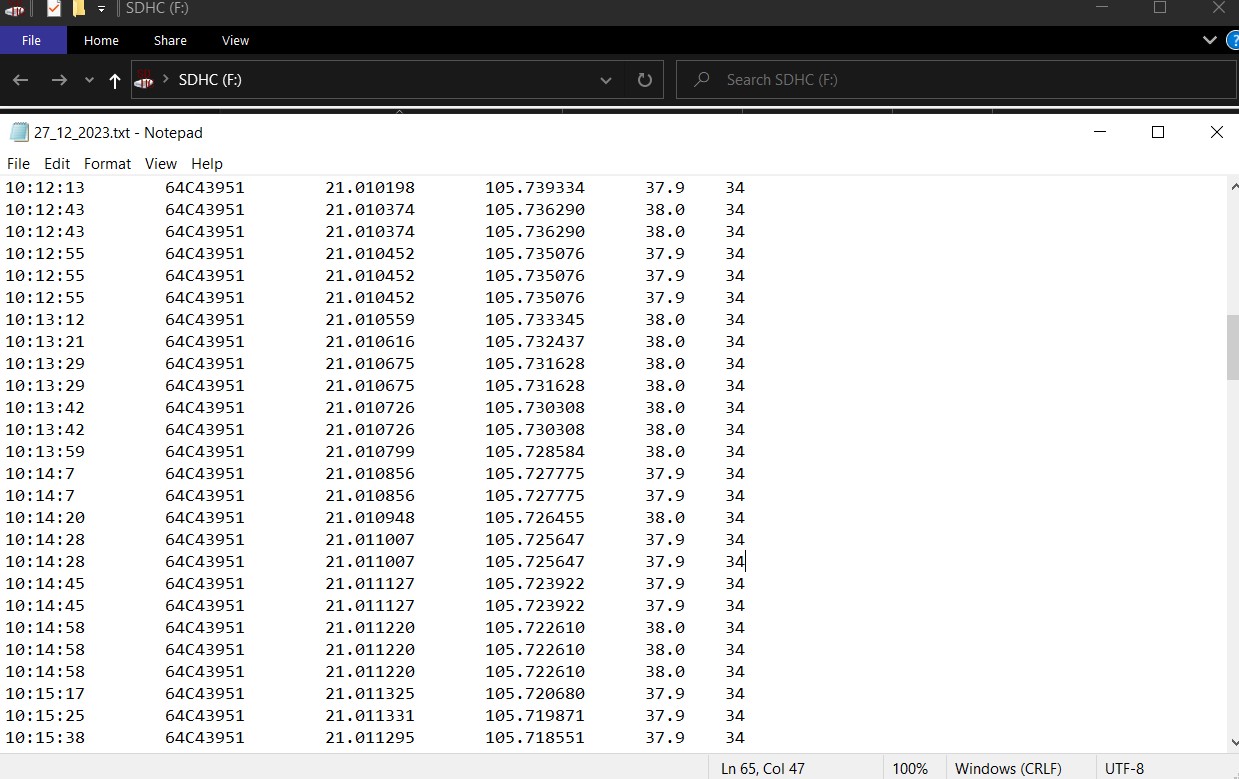
PICTURE/sdcard_file2.jpg
