huyhoanghust/Final-Project/PICTURE/sdcard_file.jpg

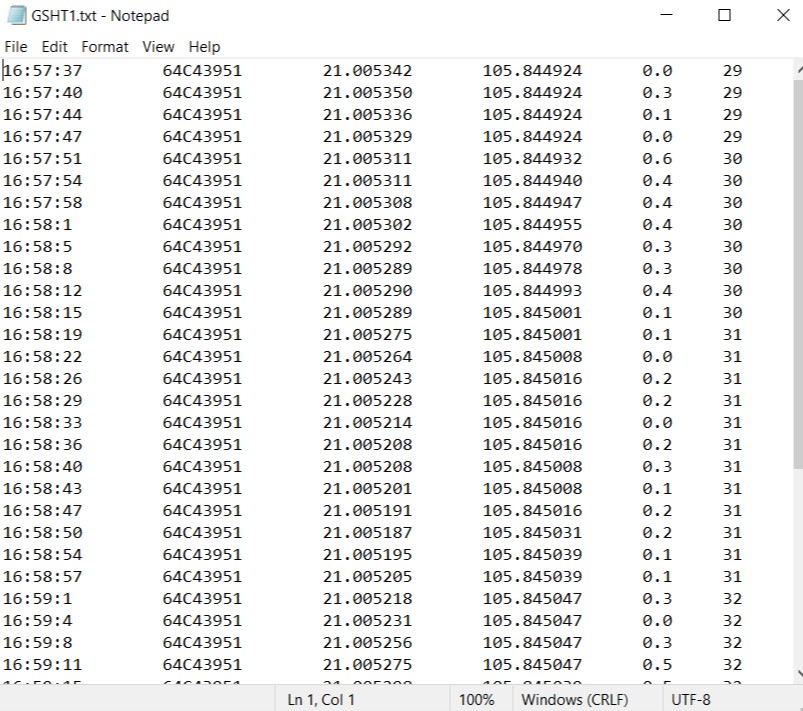
PICTURE/sdcard_file.jpg
