huyhoanghust/Final-Project/PICTURE/sim/hoạt động của sim.jpg

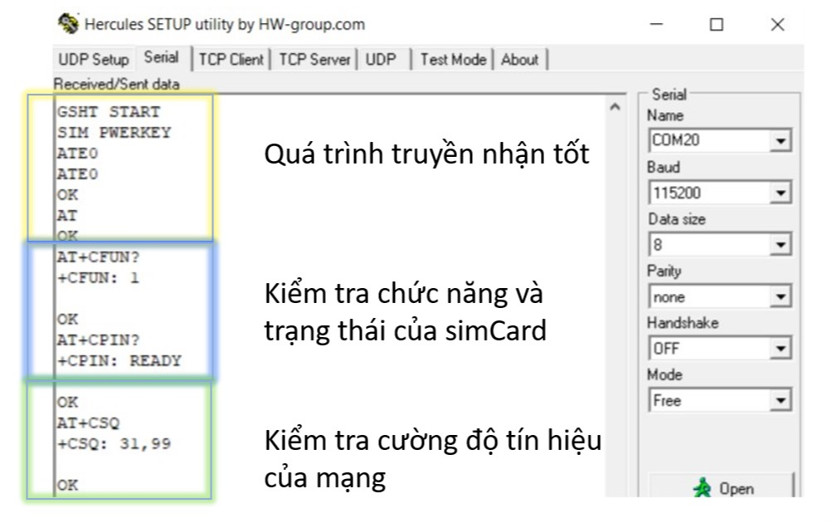
PICTURE/sim/hoạt động của sim.jpg
