huyhoanghust/Final-Project/PICTURE/sim/kết nối  mqtt.jpg

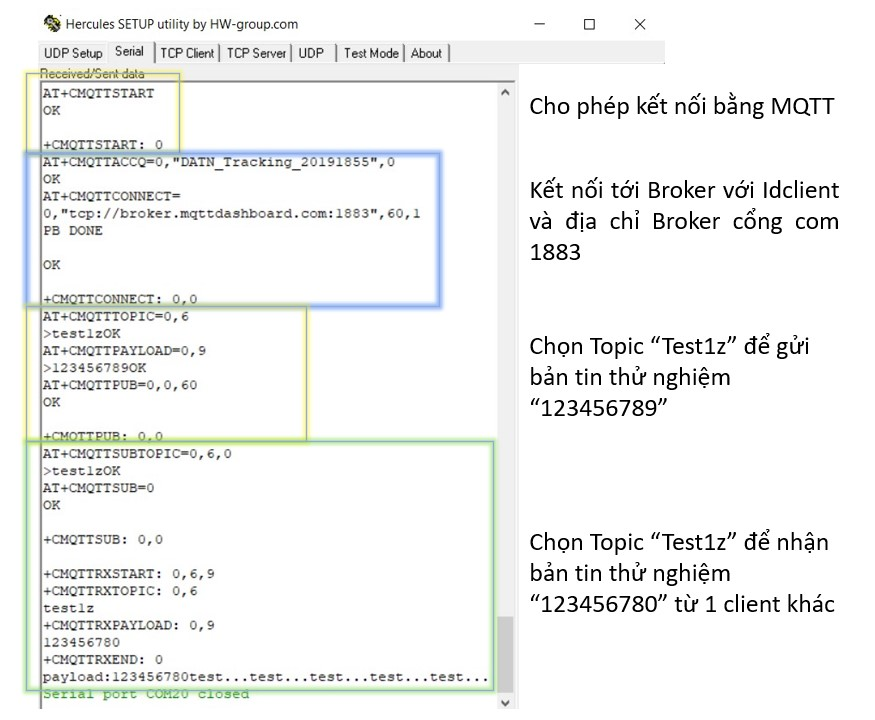
PICTURE/sim/kết nối mqtt.jpg
