huyhoanghust/Final-Project/PICTURE/sim/mqtt2.jpg

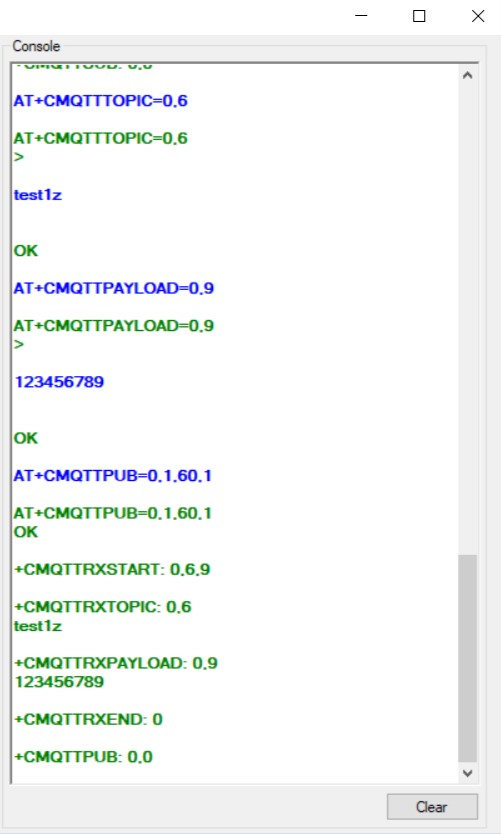
PICTURE/sim/mqtt2.jpg
