huyhoanghust/Final-Project/PICTURE/sim/mqtt3.jpg

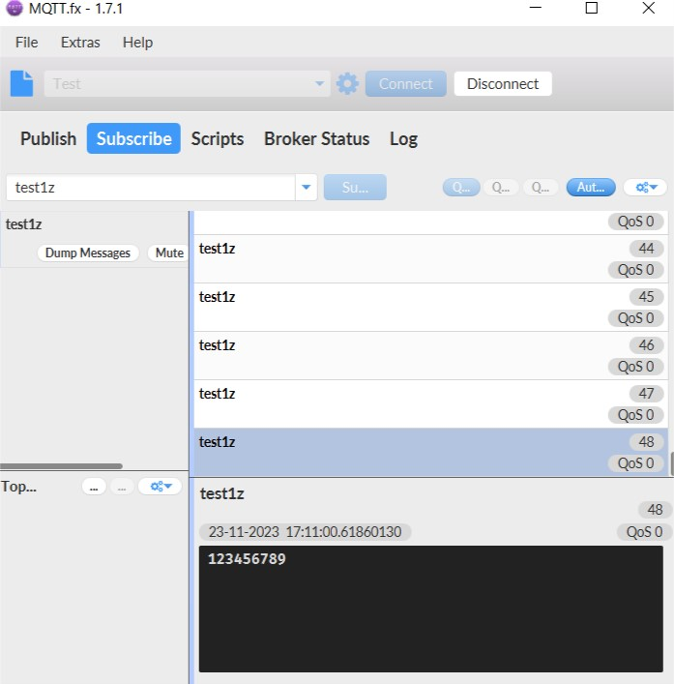
PICTURE/sim/mqtt3.jpg
