huyhoanghust/Final-Project/PICTURE/sim/mqtt_v1.jpg

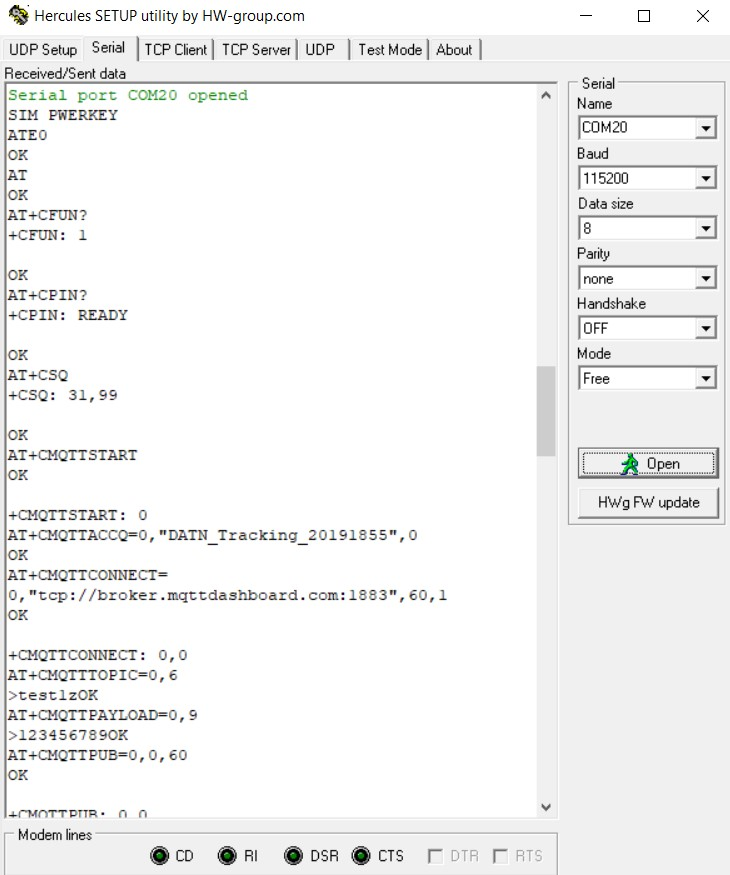
PICTURE/sim/mqtt_v1.jpg
