huyhoanghust/Final-Project/PICTURE/sim/sim 1.jpg

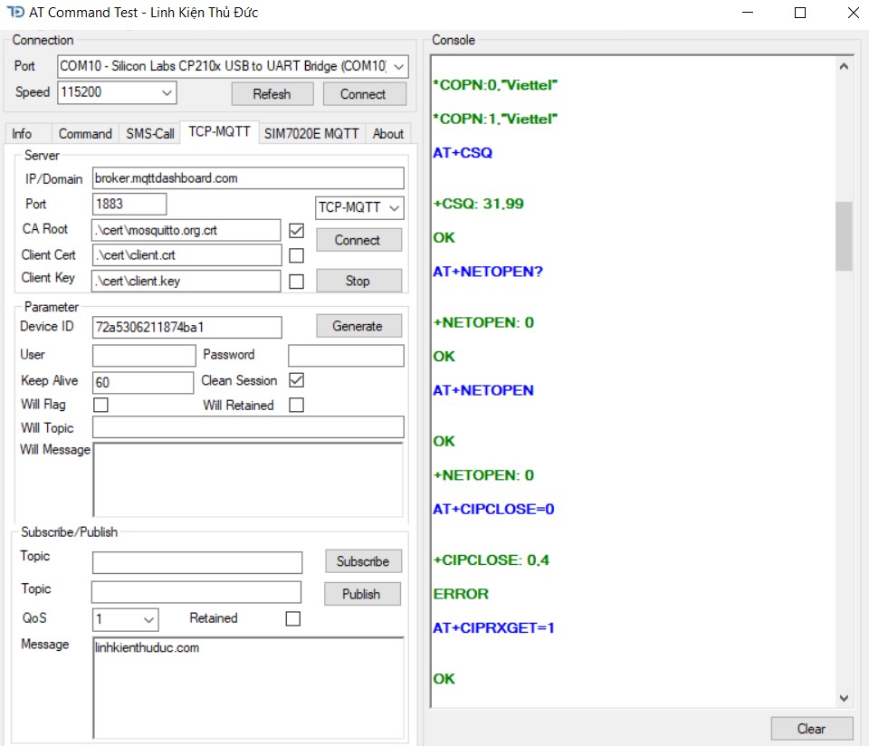
PICTURE/sim/sim 1.jpg
