huyhoanghust/Final-Project/PICTURE/sim/ĐATN-mqtt_1.drawio (1).png

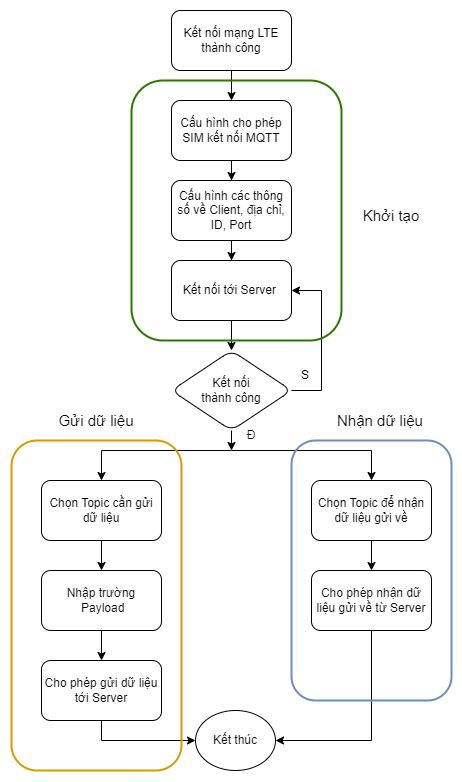
PICTURE/sim/ĐATN-mqtt_1.drawio (1).png
