huyhoanghust/Final-Project/PICTURE/sim/ĐATN-mqtt_1.drawio.png

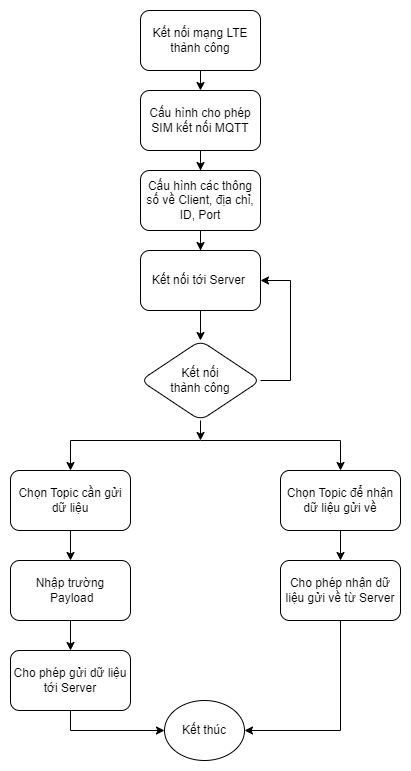
PICTURE/sim/ĐATN-mqtt_1.drawio.png
