huyhoanghust/Final-Project/PICTURE/sim/ĐATN-mqttbroker.drawio.png

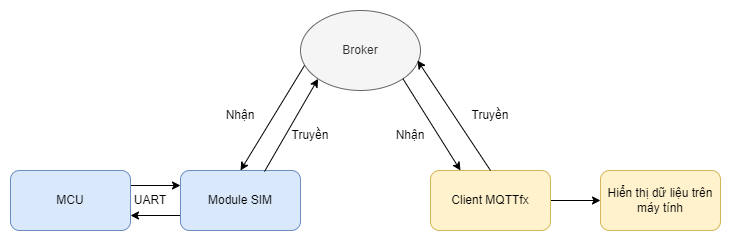
PICTURE/sim/ĐATN-mqttbroker.drawio.png
