huyhoanghust/Final-Project/PICTURE/sim/ĐATN-sim_at.drawio.png

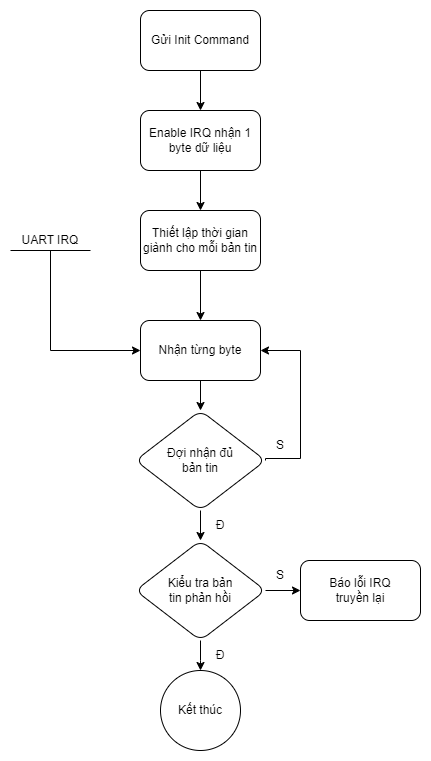
PICTURE/sim/ĐATN-sim_at.drawio.png
