huyhoanghust/Final-Project/PICTURE/Status_pin.jpg

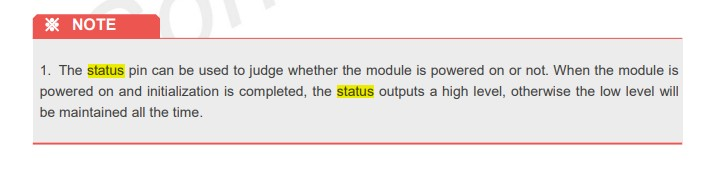
PICTURE/Status_pin.jpg
