huyhoanghust/Final-Project/PICTURE/web/cấu trúc.jpg

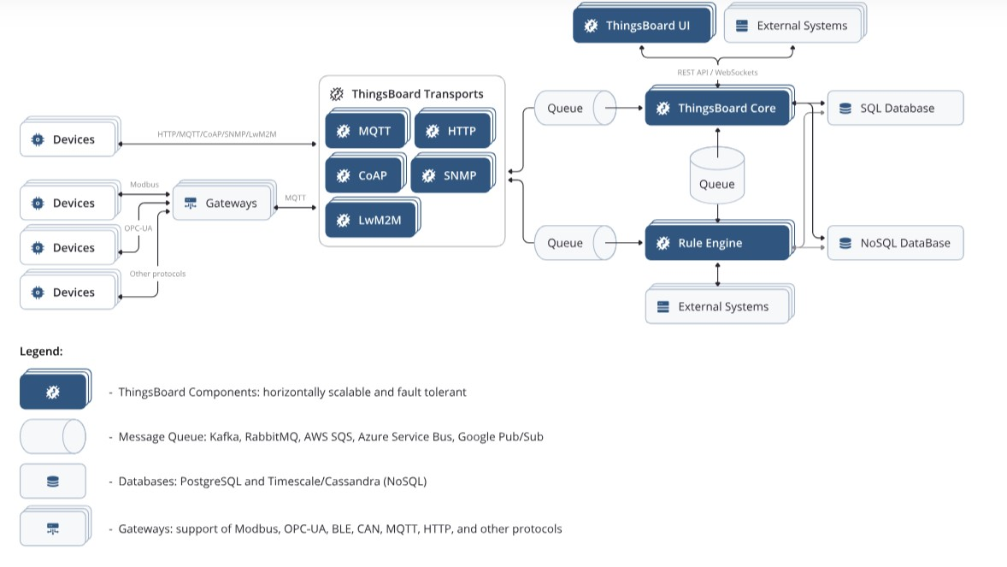
PICTURE/web/cấu trúc.jpg
