huyhoanghust/Final-Project/PICTURE/web/ĐATN-mqttbroker.drawio.png

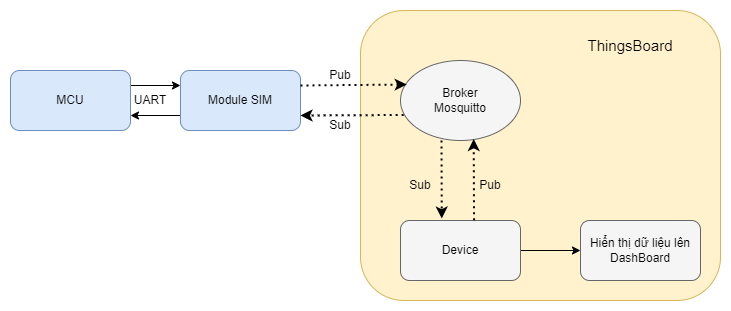
PICTURE/web/ĐATN-mqttbroker.drawio.png
