huyhoanghust/Final-Project/PICTURE/web/ĐATN-TB_1.drawio.png

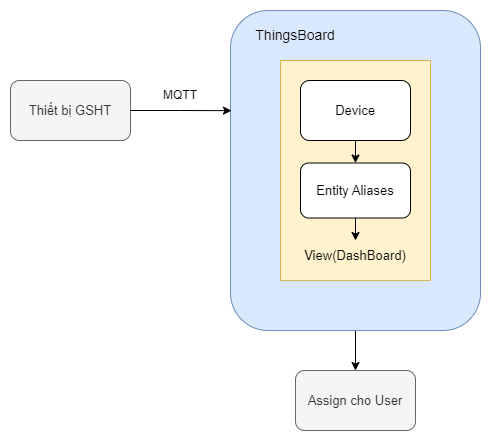
PICTURE/web/ĐATN-TB_1.drawio.png
