huyhoanghust/Final-Project/PICTURE/{44AD2381-B677-470D-A2DC-89896AF5CCB2}.png.jpg

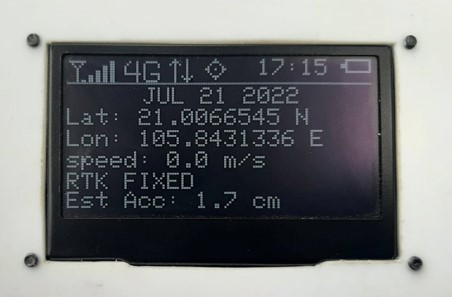
PICTURE/{44AD2381-B677-470D-A2DC-89896AF5CCB2}.png.jpg
