huyhoanghust/Final-Project/PICTURE/{EEBA371C-8C70-41ED-9442-E453F80B7D17}.png.jpg

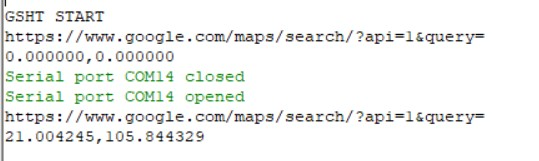
PICTURE/{EEBA371C-8C70-41ED-9442-E453F80B7D17}.png.jpg
