huyhoanghust/Final-Project/PICTURE/đo nguồn/bố trí 2.jpg

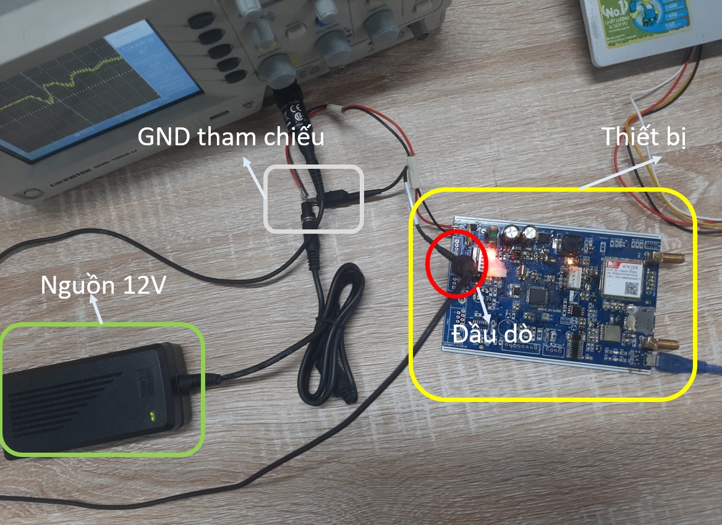
PICTURE/đo nguồn/bố trí 2.jpg
