huyhoanghust/Final-Project/PICTURE/đo nguồn/dc_12v_ldo.jpg

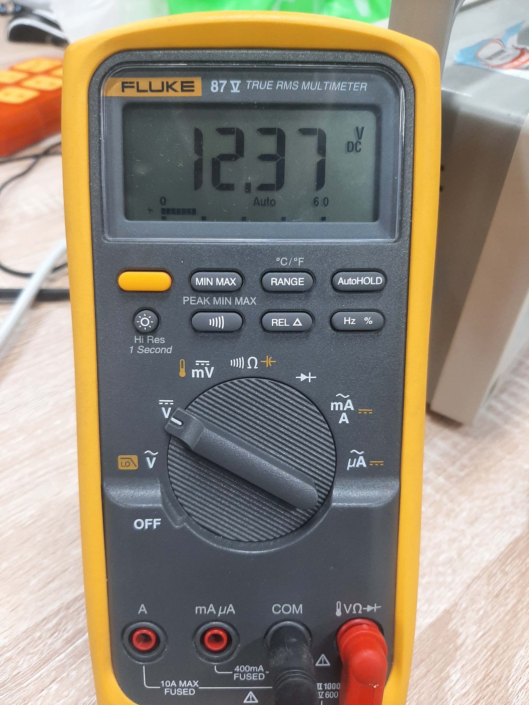
PICTURE/đo nguồn/dc_12v_ldo.jpg
