huyhoanghust/Final-Project/PICTURE/đo nguồn/ripple_5v.jpg

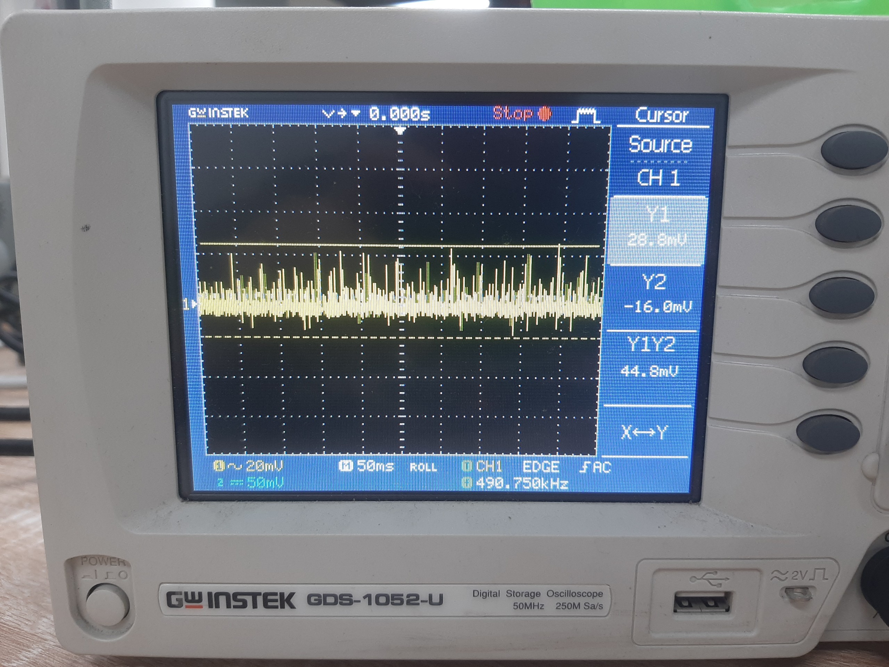
PICTURE/đo nguồn/ripple_5v.jpg
