huyhoanghust/Final-Project/PICTURE/đo nguồn/ripple_12v_ldo.jpg

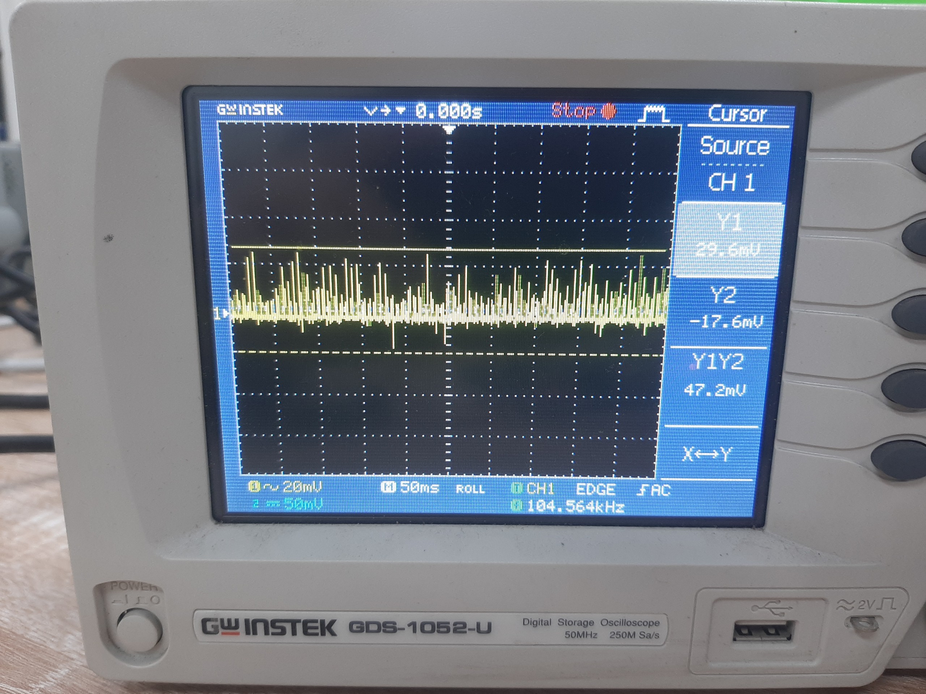
PICTURE/đo nguồn/ripple_12v_ldo.jpg
