huyhoanghust/Final-Project/PICTURE/đo nguồn/ripple_12v_nguon.jpg

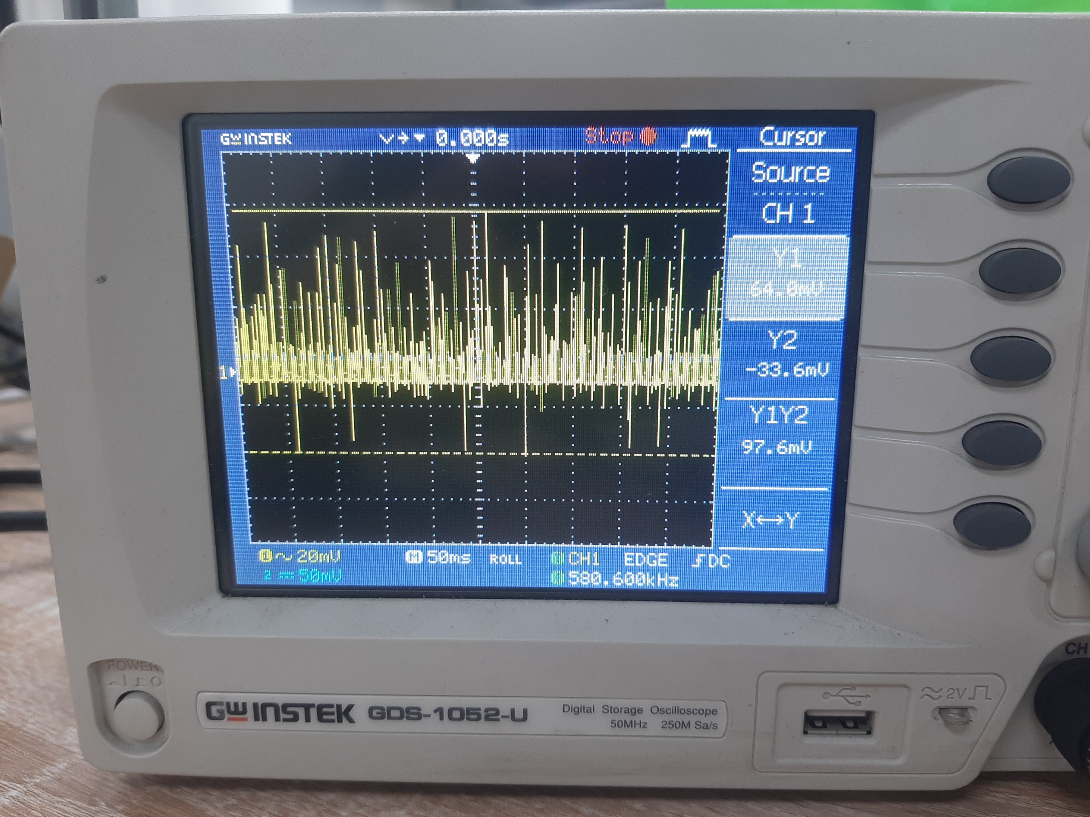
PICTURE/đo nguồn/ripple_12v_nguon.jpg
