huyhoanghust/Final-Project/PICTURE/đo nguồn/ripple_sim.jpg

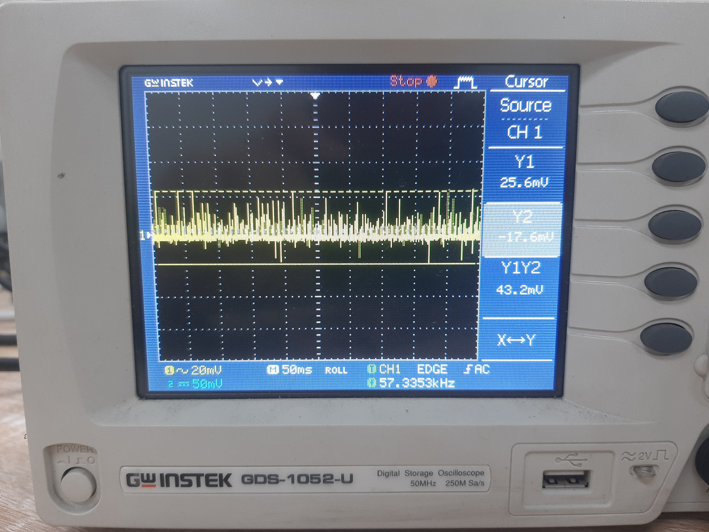
PICTURE/đo nguồn/ripple_sim.jpg
