huyhoanghust/Final-Project/PICTURE/đo nguồn/ripplee_gnss.jpg

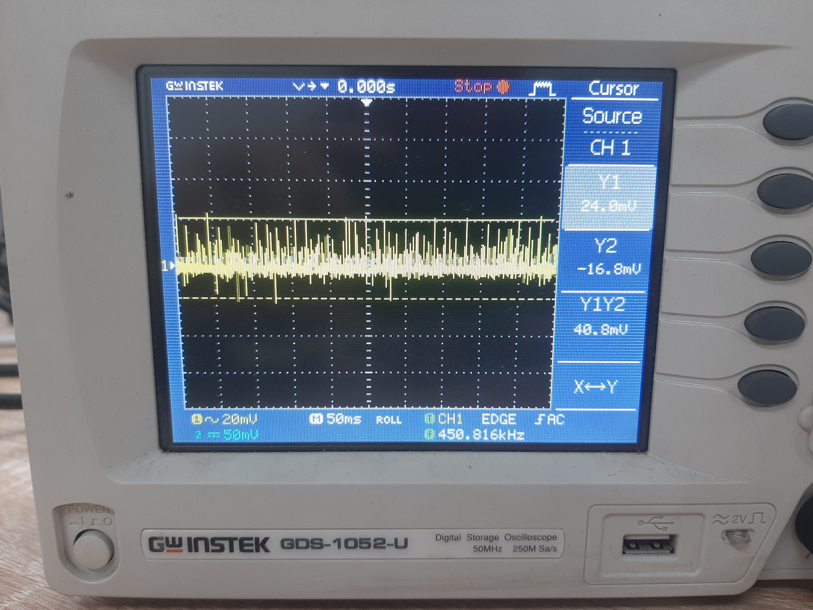
PICTURE/đo nguồn/ripplee_gnss.jpg
