huyhoanghust/Final-Project/PICTURE/đo nguồn/tool.jpg

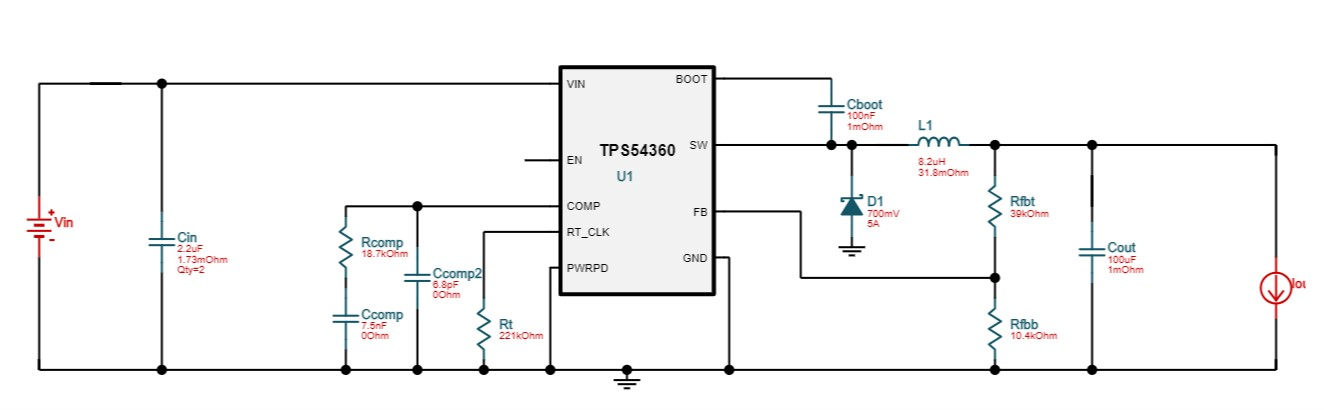
PICTURE/đo nguồn/tool.jpg
