huyhoanghust/Final-Project/PICTURE/đo nguồn/{71CD243F-E17D-4947-88BB-47F4EC0A559C}.png.jpg

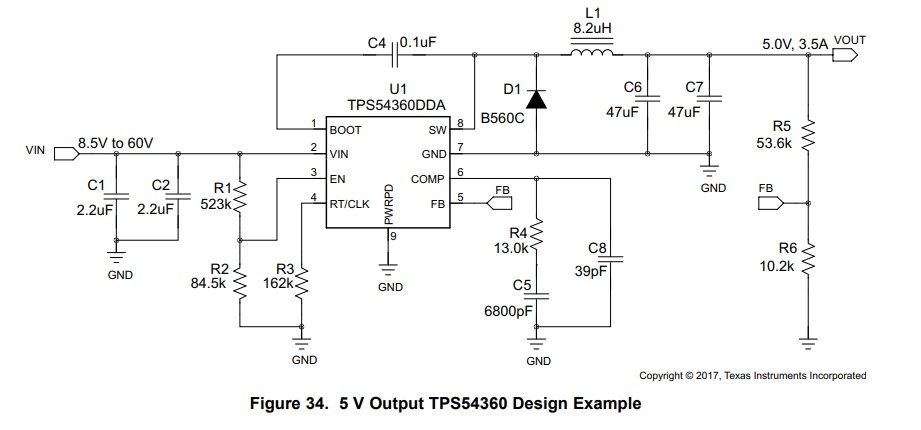
PICTURE/đo nguồn/{71CD243F-E17D-4947-88BB-47F4EC0A559C}.png.jpg
