huyhoanghust/Final-Project/ĐATN-vỏ_lắp trên.drawio.png

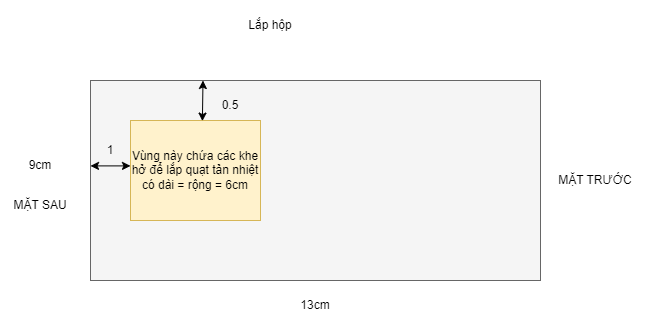
ĐATN-vỏ_lắp trên.drawio.png
