huyhoanghust/Final-Project/ĐATN-vỏ_sau.drawio.png

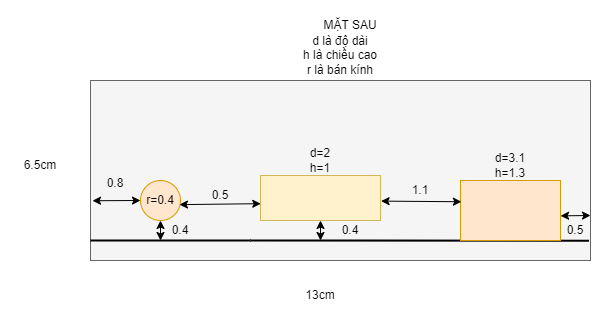
ĐATN-vỏ_sau.drawio.png
