huyhoanghust/Final-Project/ĐATN-vỏ_trước.drawio.png

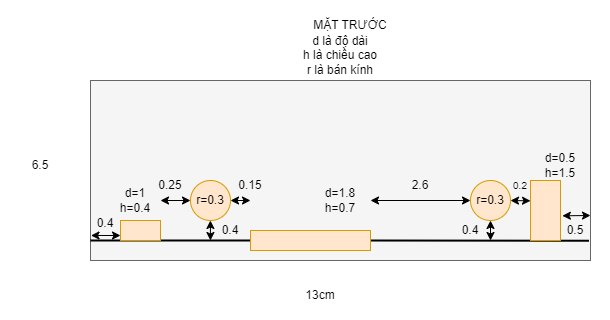
ĐATN-vỏ_trước.drawio.png
