huyhoanghust/Final-Project/ĐATN-vỏ_đáy hộp.drawio.png

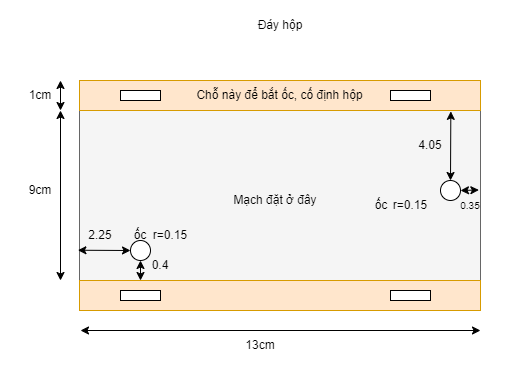
ĐATN-vỏ_đáy hộp.drawio.png
