huyhoanghust/Final-Project/FIRMWARE/FIRMWARE_CUBE/Core/Src/rtc.c

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
/* Includes ------------------------------------------------------------------*/
#include "rtc.h"

/* USER CODE BEGIN 0 */
void rtc_init()
{
  hrtc.Instance = RTC;
  hrtc.Init.AsynchPrediv = RTC_AUTO_1_SECOND;
  hrtc.Init.OutPut = RTC_OUTPUTSOURCE_ALARM;
  if (HAL_RTC_Init(&hrtc) != HAL_OK)
  {
    Error_Handler();
  }
}

void rtc_set_time()
{
  RTC_TimeTypeDef sTime = {0};
  RTC_DateTypeDef DateToUpdate = {0};
  sTime.Hours = 0x10;
  sTime.Minutes = 0x0;
  sTime.Seconds = 0x0;

  if (HAL_RTC_SetTime(&hrtc, &sTime, RTC_FORMAT_BCD) != HAL_OK)
  {
    Error_Handler();
  }
  DateToUpdate.WeekDay = RTC_WEEKDAY_MONDAY;
  DateToUpdate.Month = RTC_MONTH_JANUARY;
  DateToUpdate.Date = 0x1;
  DateToUpdate.Year = 0x0;

  if (HAL_RTC_SetDate(&hrtc, &DateToUpdate, RTC_FORMAT_BCD) != HAL_OK)
  {
    Error_Handler();
  }
  HAL_RTCEx_BKUPWrite(&hrtc, RTC_BKP_DR1, 0x32F2); // backup register
}

void rtc_set_alarm(RTC_TimeTypeDef *sTime)
{
  RTC_AlarmTypeDef sAlarm = {0};
  sAlarm.AlarmTime.Hours = sTime->Hours;
  sAlarm.AlarmTime.Minutes = sTime->Minutes;
  sAlarm.AlarmTime.Seconds = sTime->Seconds + 5;
  sAlarm.Alarm = RTC_ALARM_A;
  if (HAL_RTC_SetAlarm(&hrtc, &sAlarm, RTC_FORMAT_BCD) != HAL_OK)
  {
    Error_Handler();
  }
}

void rtc_get_time(RTC_TimeTypeDef *sTime, RTC_DateTypeDef *sDate)
{
  HAL_RTC_GetTime(&hrtc, &sTime, RTC_FORMAT_BIN);
  HAL_RTC_GetDate(&hrtc, &sDate, RTC_FORMAT_BIN);
}
/* USER CODE END 0 */

RTC_HandleTypeDef hrtc;

/* RTC init function */
void MX_RTC_Init(void)
{

  RTC_TimeTypeDef sTime = {0};
  RTC_DateTypeDef DateToUpdate = {0};
  RTC_AlarmTypeDef sAlarm = {0};

  /** Initialize RTC Only
  */
  hrtc.Instance = RTC;
  hrtc.Init.AsynchPrediv = RTC_AUTO_1_SECOND;
  hrtc.Init.OutPut = RTC_OUTPUTSOURCE_ALARM;
  if (HAL_RTC_Init(&hrtc) != HAL_OK)
  {
    Error_Handler();
  }

  /** Initialize RTC and set the Time and Date
  */
  sTime.Hours = 0x10;
  sTime.Minutes = 0x0;
  sTime.Seconds = 0x0;

  if (HAL_RTC_SetTime(&hrtc, &sTime, RTC_FORMAT_BCD) != HAL_OK)
  {
    Error_Handler();
  }
  DateToUpdate.WeekDay = RTC_WEEKDAY_MONDAY;
  DateToUpdate.Month = RTC_MONTH_JANUARY;
  DateToUpdate.Date = 0x1;
  DateToUpdate.Year = 0x23;

  if (HAL_RTC_SetDate(&hrtc, &DateToUpdate, RTC_FORMAT_BCD) != HAL_OK)
  {
    Error_Handler();
  }

  /** Enable the Alarm A
  */
  sAlarm.AlarmTime.Hours = 0x0;
  sAlarm.AlarmTime.Minutes = 0x0;
  sAlarm.AlarmTime.Seconds = 0x0;
  sAlarm.Alarm = RTC_ALARM_A;
  if (HAL_RTC_SetAlarm_IT(&hrtc, &sAlarm, RTC_FORMAT_BCD) != HAL_OK)
  {
    Error_Handler();
  }
}

void HAL_RTC_MspInit(RTC_HandleTypeDef* rtcHandle)
{

  if(rtcHandle->Instance==RTC)
  {
    HAL_PWR_EnableBkUpAccess();
    /* Enable BKP CLK enable for backup registers */
    __HAL_RCC_BKP_CLK_ENABLE();
    /* RTC clock enable */
    __HAL_RCC_RTC_ENABLE();

    /* RTC interrupt Init */
    HAL_NVIC_SetPriority(RTC_IRQn, 0, 0);
    HAL_NVIC_EnableIRQ(RTC_IRQn);
    HAL_NVIC_SetPriority(RTC_Alarm_IRQn, 0, 0);
    HAL_NVIC_EnableIRQ(RTC_Alarm_IRQn);
  }
}

void HAL_RTC_MspDeInit(RTC_HandleTypeDef* rtcHandle)
{

  if(rtcHandle->Instance==RTC)
  {
    /* Peripheral clock disable */
    __HAL_RCC_RTC_DISABLE();

    /* RTC interrupt Deinit */
    HAL_NVIC_DisableIRQ(RTC_IRQn);
    HAL_NVIC_DisableIRQ(RTC_Alarm_IRQn);
  }
}
